RndMnkIII/Analogizer/case_mounting/1722326016145.jpg

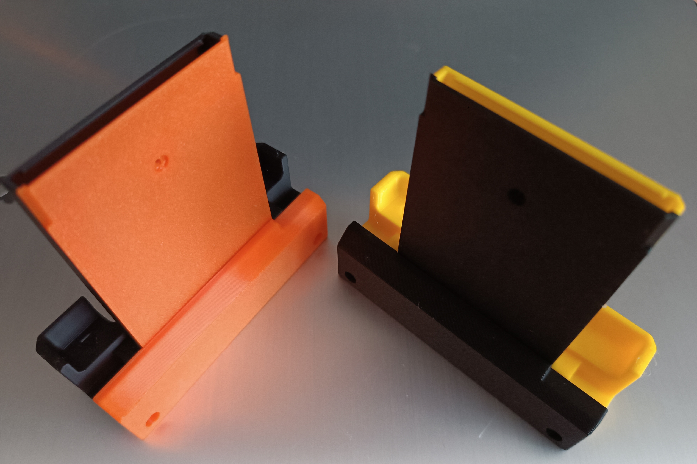
case_mounting/1722326016145.jpg
