RndMnkIII/Analogizer/case_mounting/1722326016159.jpg

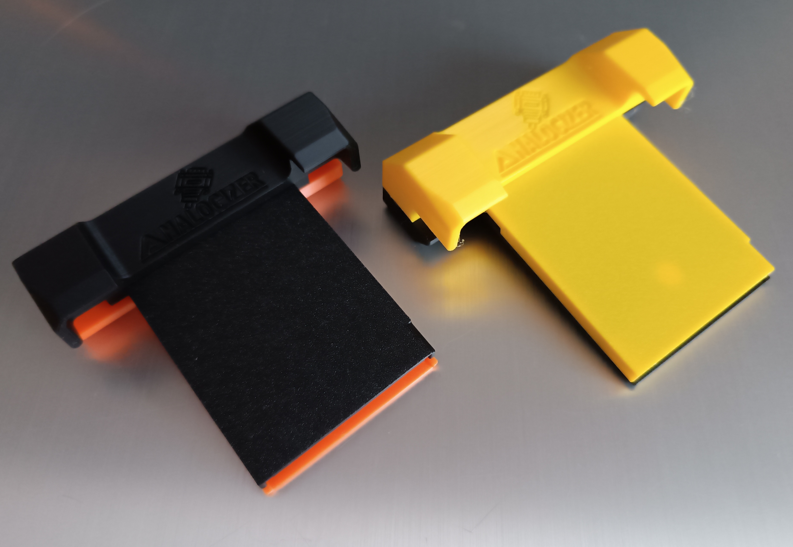
case_mounting/1722326016159.jpg
