RndMnkIII/Analogizer/case_mounting/1722326016175.jpg

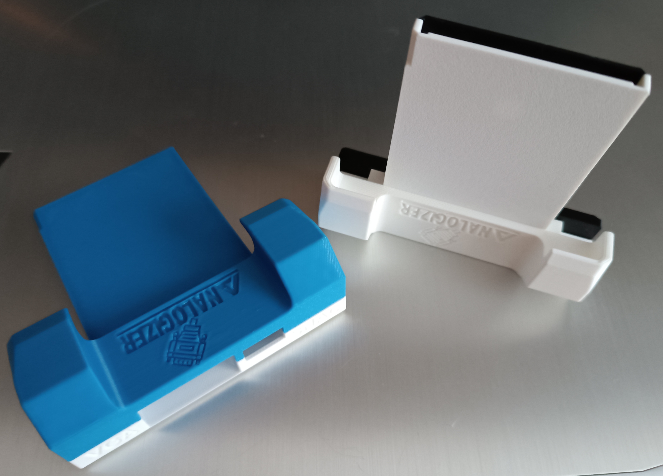
case_mounting/1722326016175.jpg
