RndMnkIII/Analogizer/case_mounting/1722326016191.jpg

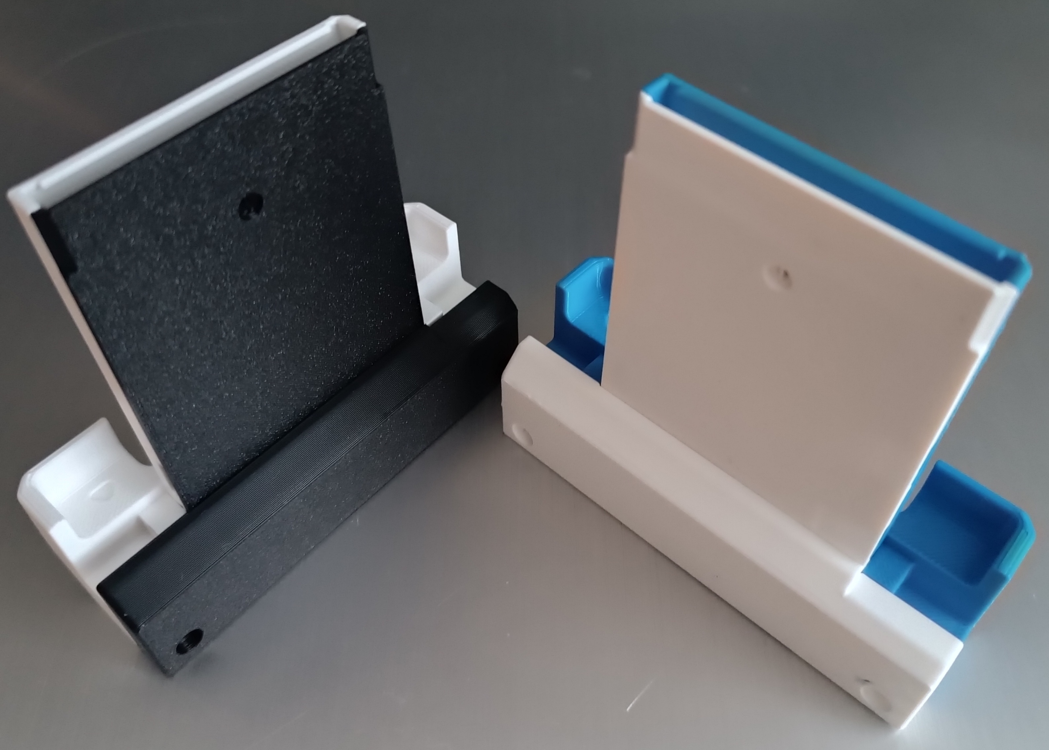
case_mounting/1722326016191.jpg
