RndMnkIII/Analogizer/case_mounting/1722326016210.jpg

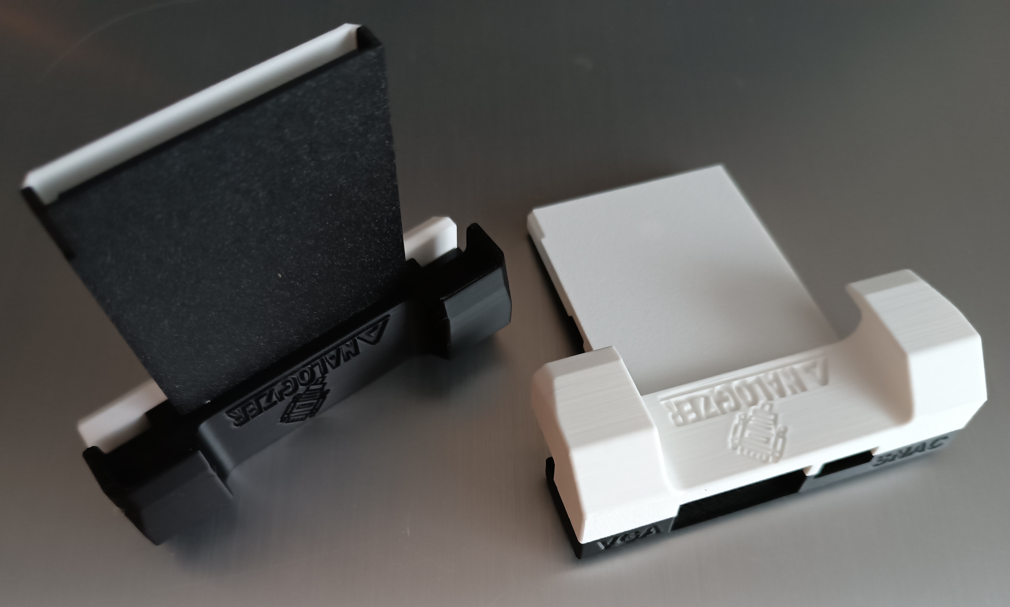
case_mounting/1722326016210.jpg
