RndMnkIII/Analogizer/case_mounting/1722352187809.jpg

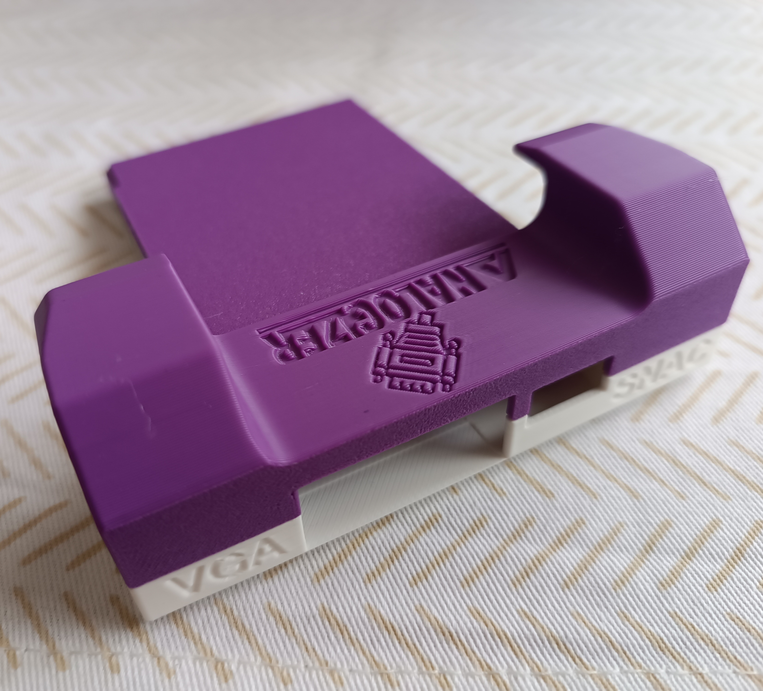
case_mounting/1722352187809.jpg
