RndMnkIII/Analogizer/case_mounting/1722352187818.jpg

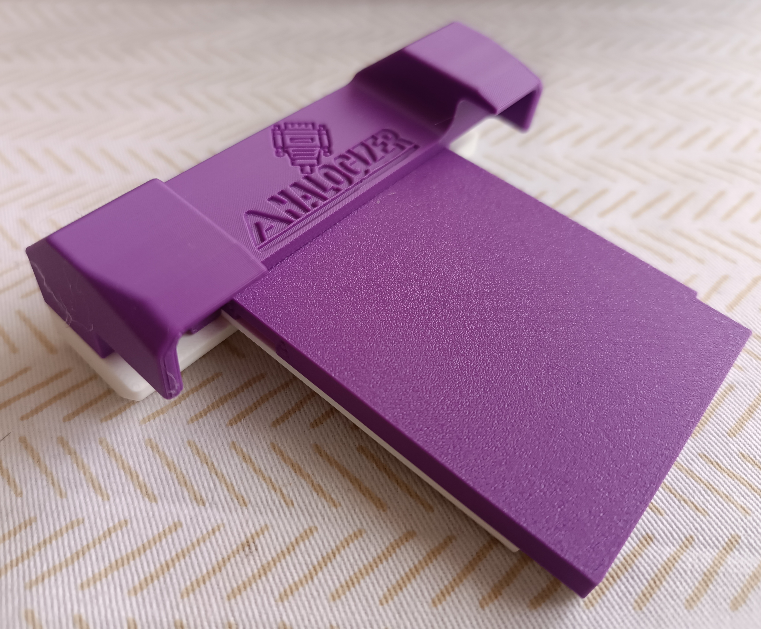
case_mounting/1722352187818.jpg
