RndMnkIII/Analogizer/case_mounting/1722352187828.jpg

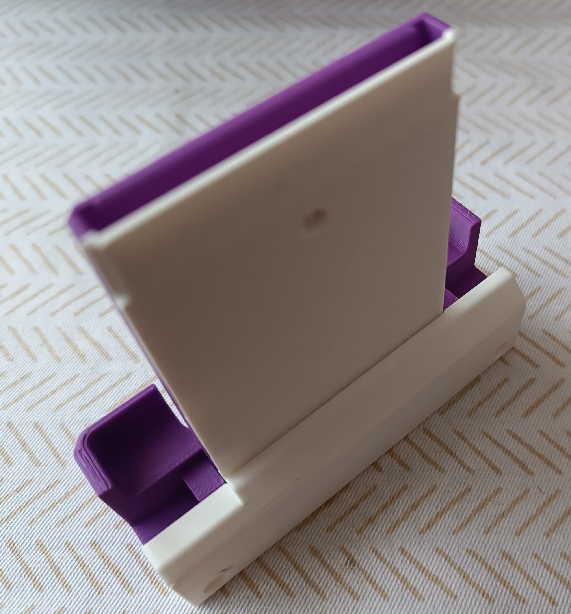
case_mounting/1722352187828.jpg
