RndMnkIII/Analogizer/case_mounting/1722354113847.jpg

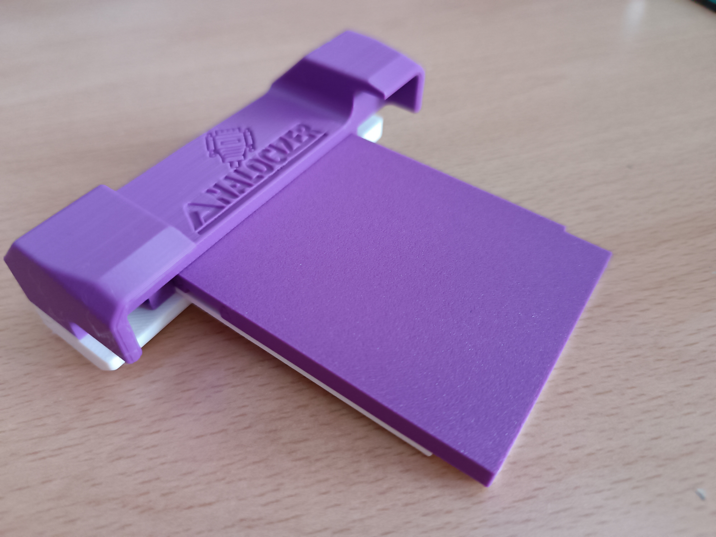
case_mounting/1722354113847.jpg
