RndMnkIII/Analogizer/case_mounting/1722354113891.jpg

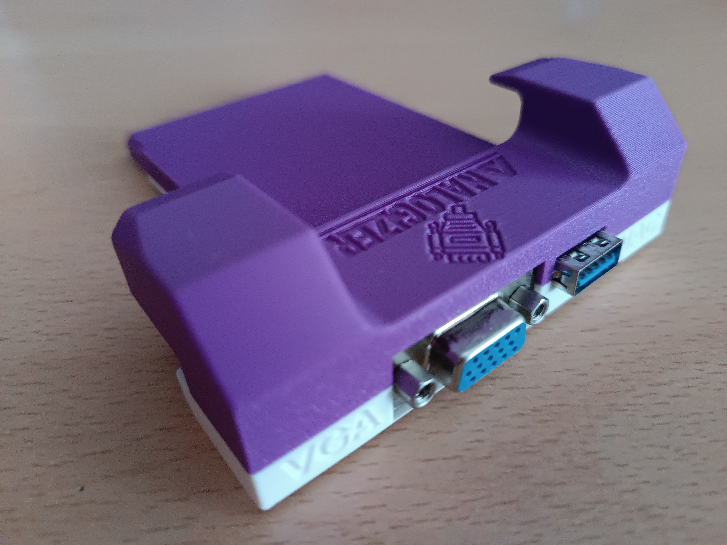
case_mounting/1722354113891.jpg
