RndMnkIII/Analogizer/hardware/SCH/PCENGINE_CABLE_HARNESS_SCH.PNG

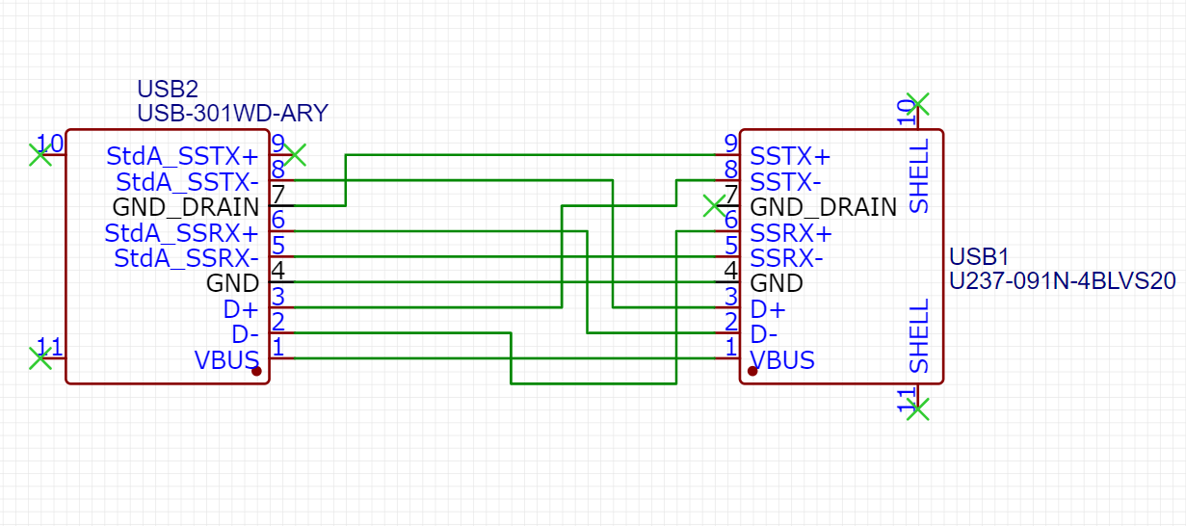
hardware/SCH/PCENGINE_CABLE_HARNESS_SCH.PNG
