RndMnkIII/Analogizer/hardware/SEGA_Genesis_Cable_harness/Captura de pantalla 2026-07-21 204106.png

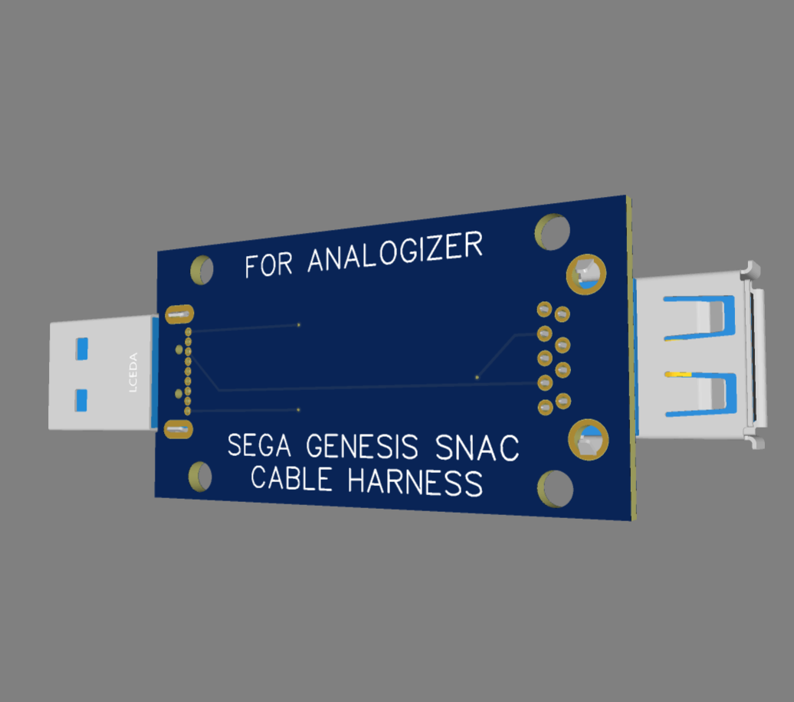
hardware/SEGA_Genesis_Cable_harness/Captura de pantalla 2026-07-21 204106.png
