RndMnkIII/Analogizer/hardware/SEGA_Genesis_Cable_harness/schematic.png

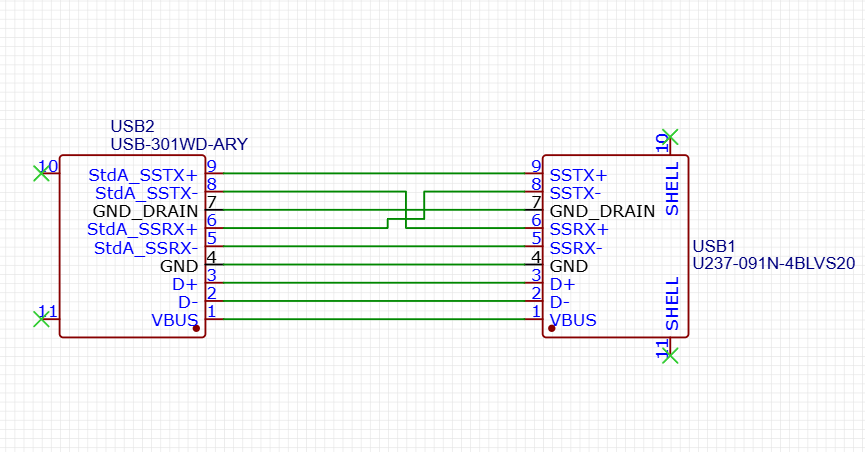
hardware/SEGA_Genesis_Cable_harness/schematic.png
