RndMnkIII/Analogizer/img/3D_PCB_HARNESS.PNG

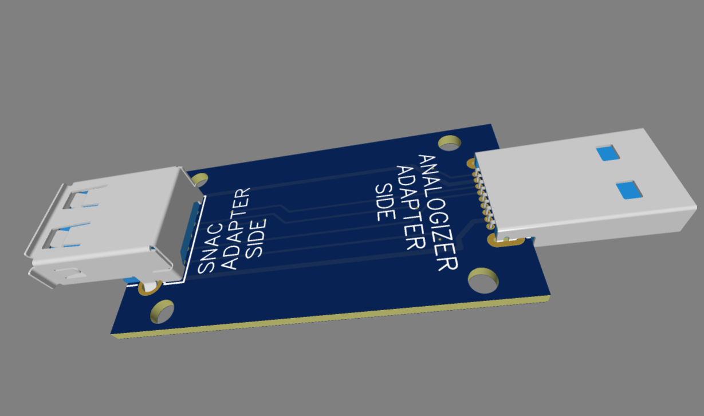
img/3D_PCB_HARNESS.PNG
