RndMnkIII/Analogizer/img/1710557132168.jpg

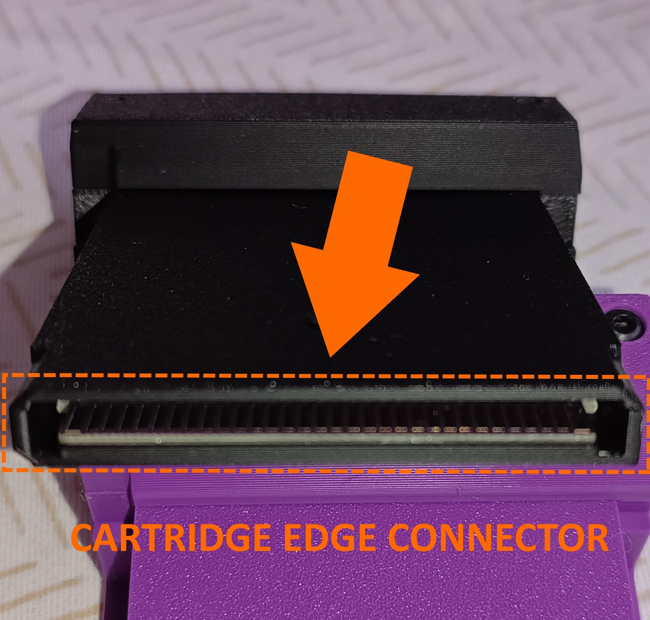
img/1710557132168.jpg
