RndMnkIII/Analogizer/img/1711795943821.jpg

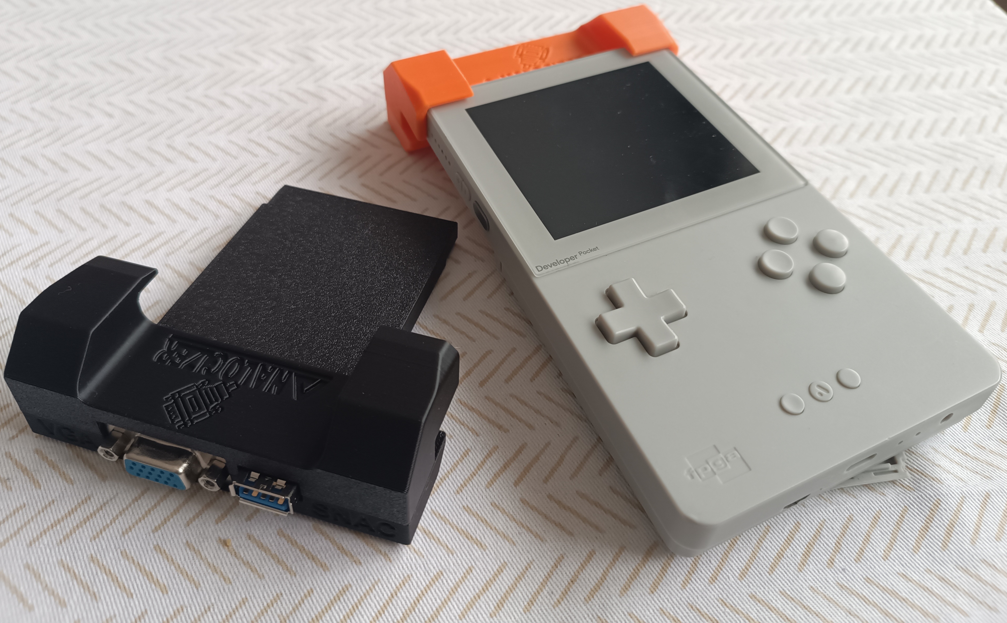
img/1711795943821.jpg
