RndMnkIII/Analogizer/img/1712216898707.jpg

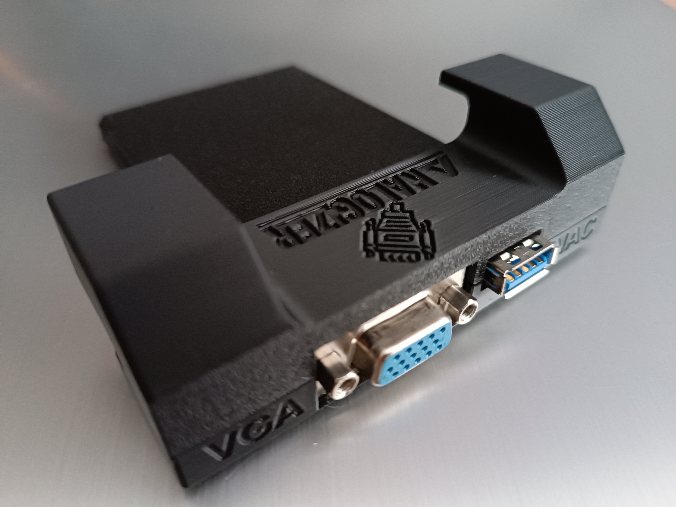
img/1712216898707.jpg
