RndMnkIII/Analogizer/img/1713608049392.jpg

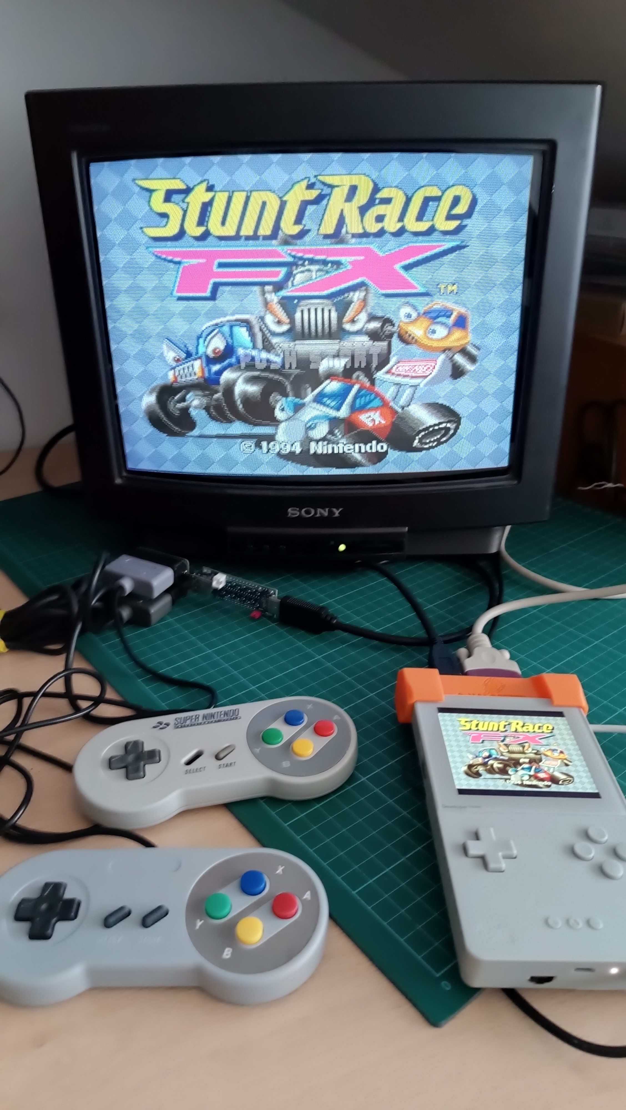
img/1713608049392.jpg
