RndMnkIII/Analogizer/img/1719057492224.jpg

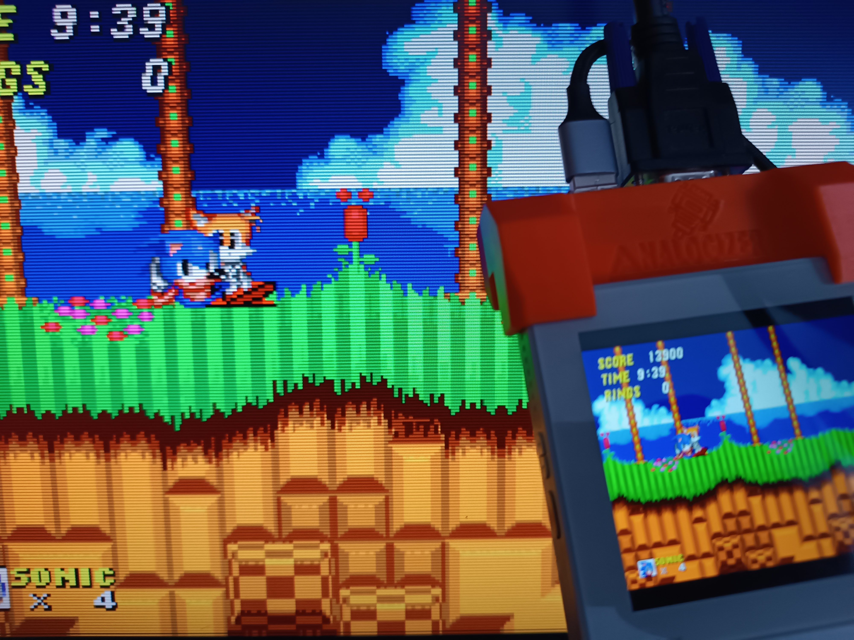
img/1719057492224.jpg
