RndMnkIII/Analogizer/img/1738831503520.jpg

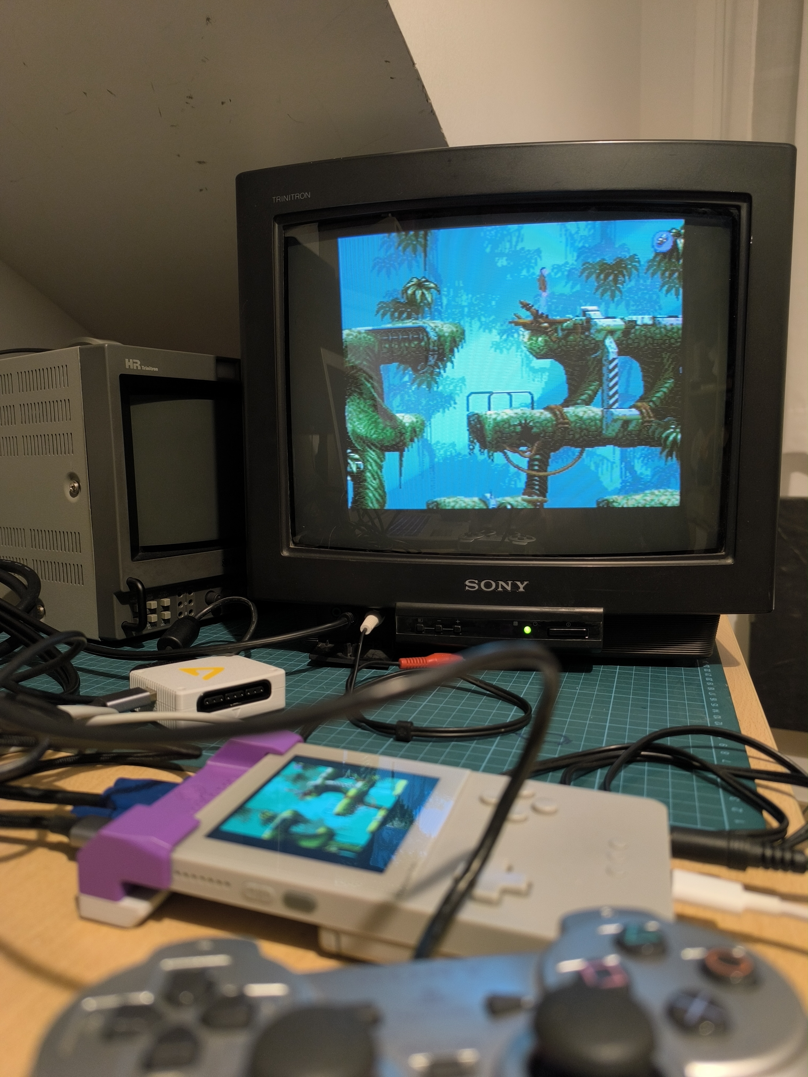
img/1738831503520.jpg
