RndMnkIII/Analogizer/img/A_nalogizer.png

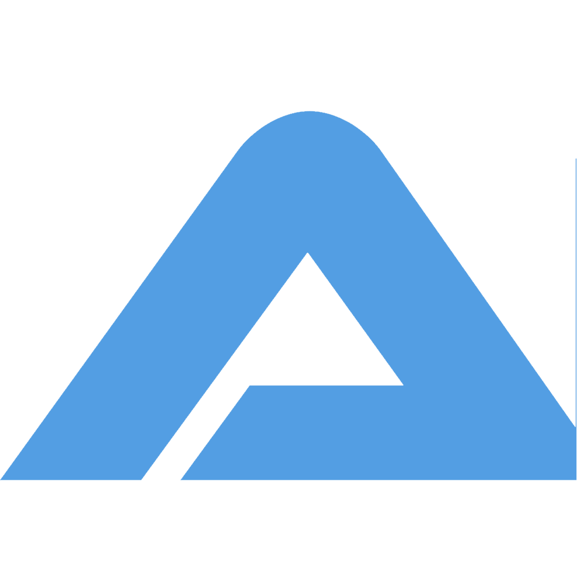
img/A_nalogizer.png
