RndMnkIII/Analogizer/img/ANALOGIZER_FRONT_SIDE.jpg

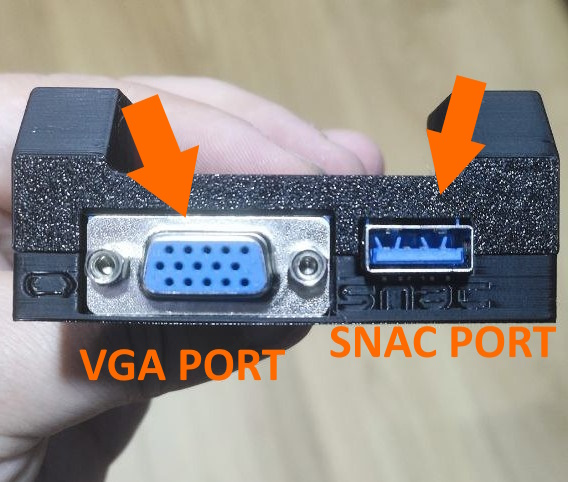
img/ANALOGIZER_FRONT_SIDE.jpg
