RndMnkIII/Analogizer/img/ANALOGIZER_SWITCH_AB.jpg

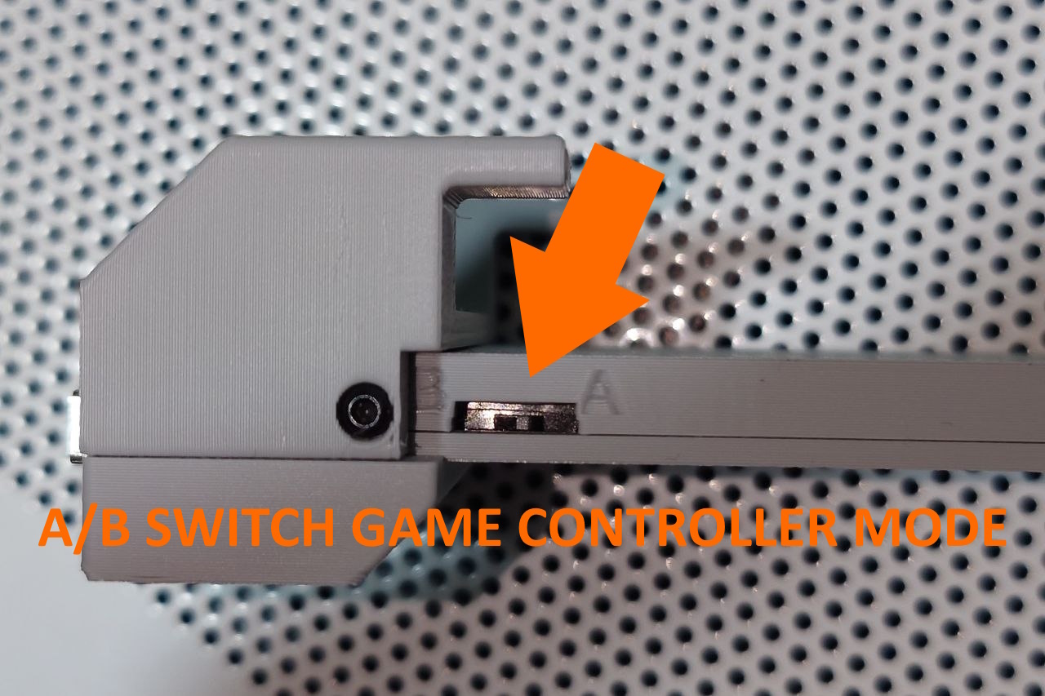
img/ANALOGIZER_SWITCH_AB.jpg
