RndMnkIII/Analogizer/img/ANALOGIZER_USB_C_PWR.jpg

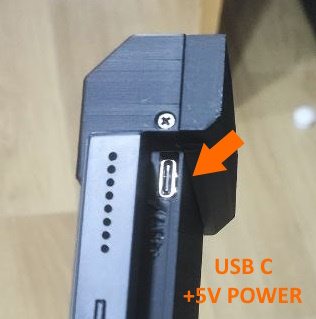
img/ANALOGIZER_USB_C_PWR.jpg
