RndMnkIII/Analogizer/img/antonio_villena_SNAC7_USB3_ADAPTERS.jpg

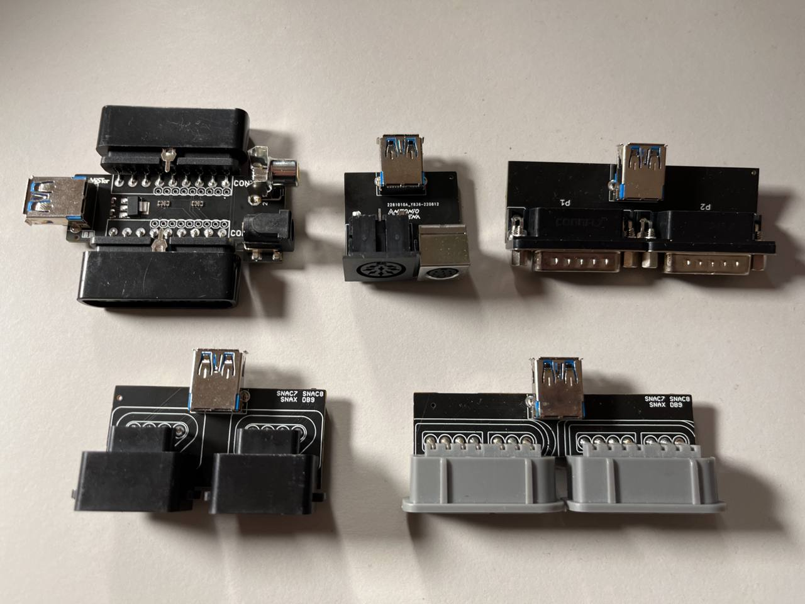
img/antonio_villena_SNAC7_USB3_ADAPTERS.jpg
