RndMnkIII/Analogizer/img/audio_jack.png

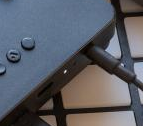
img/audio_jack.png
