RndMnkIII/Analogizer/img/cable_RGB_LINE_AUDIO_TO_SCART.PNG

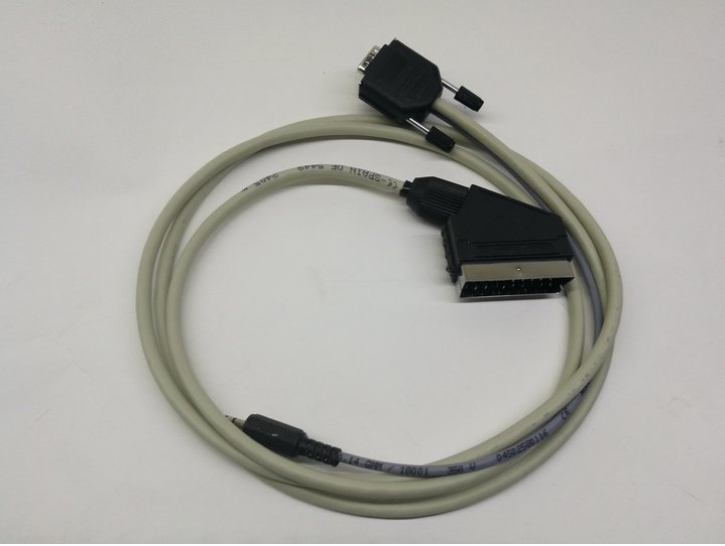
img/cable_RGB_LINE_AUDIO_TO_SCART.PNG
