RndMnkIII/Analogizer/img/como_conectar_cable_harness.jpg

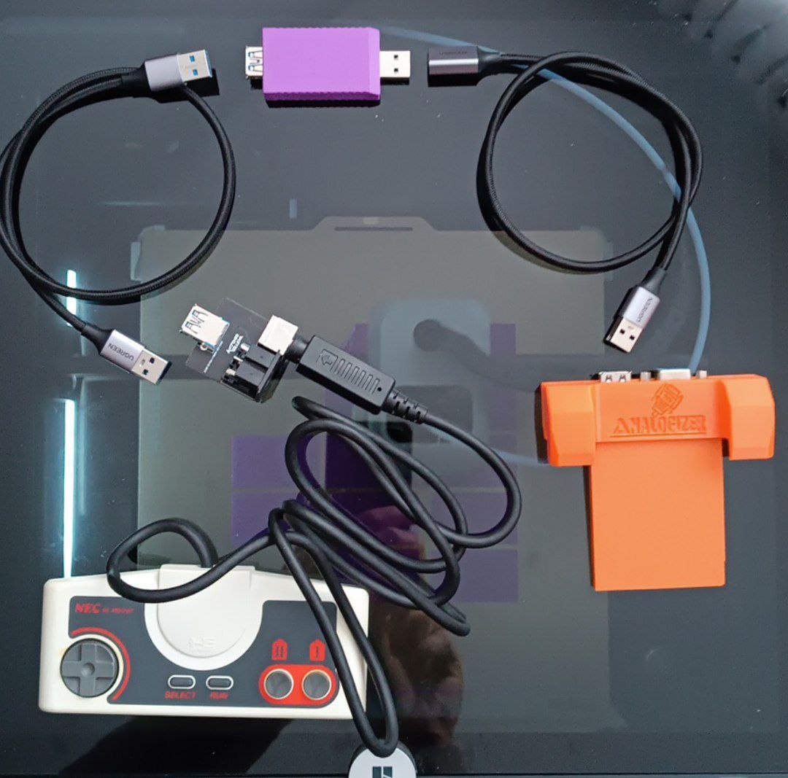
img/como_conectar_cable_harness.jpg
