RndMnkIII/Analogizer/img/cps1_analogizer.jpg

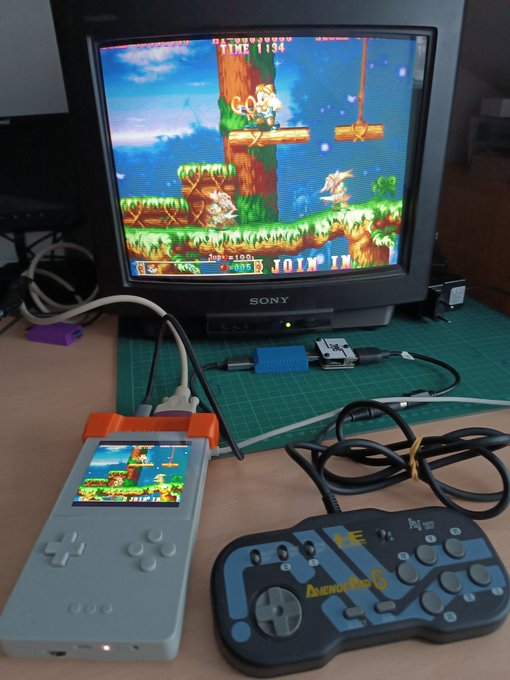
img/cps1_analogizer.jpg
