RndMnkIII/Analogizer/img/GanGeek_Style_video.png

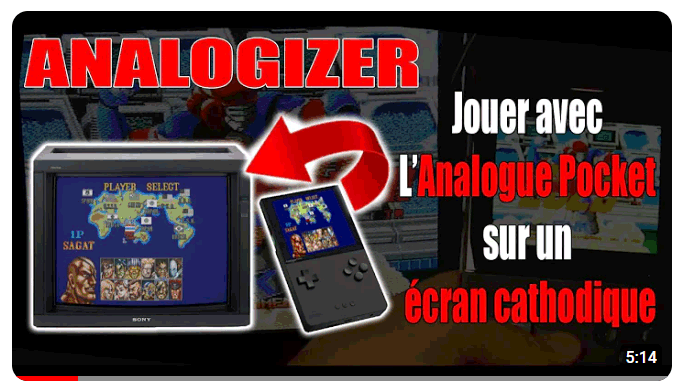
img/GanGeek_Style_video.png
