RndMnkIII/Analogizer/img/INSERT1.jpg

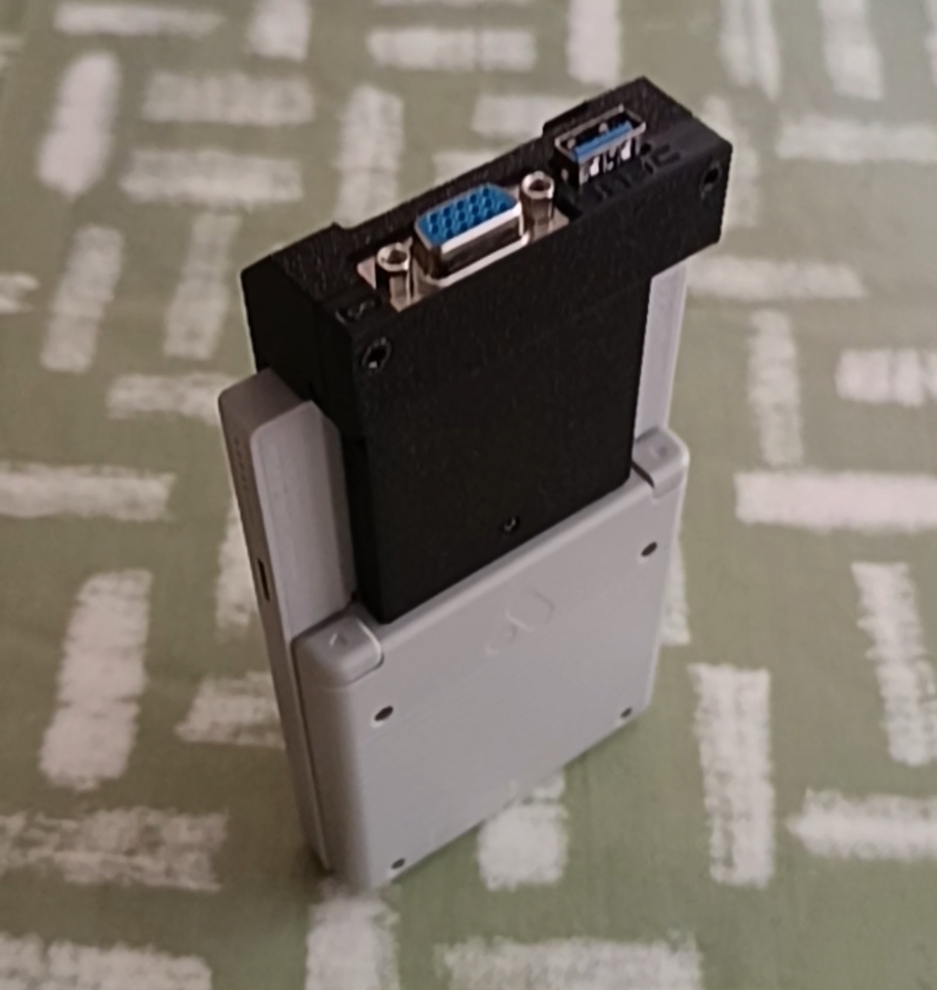
img/INSERT1.jpg
