RndMnkIII/Analogizer/img/INSERT2.jpg

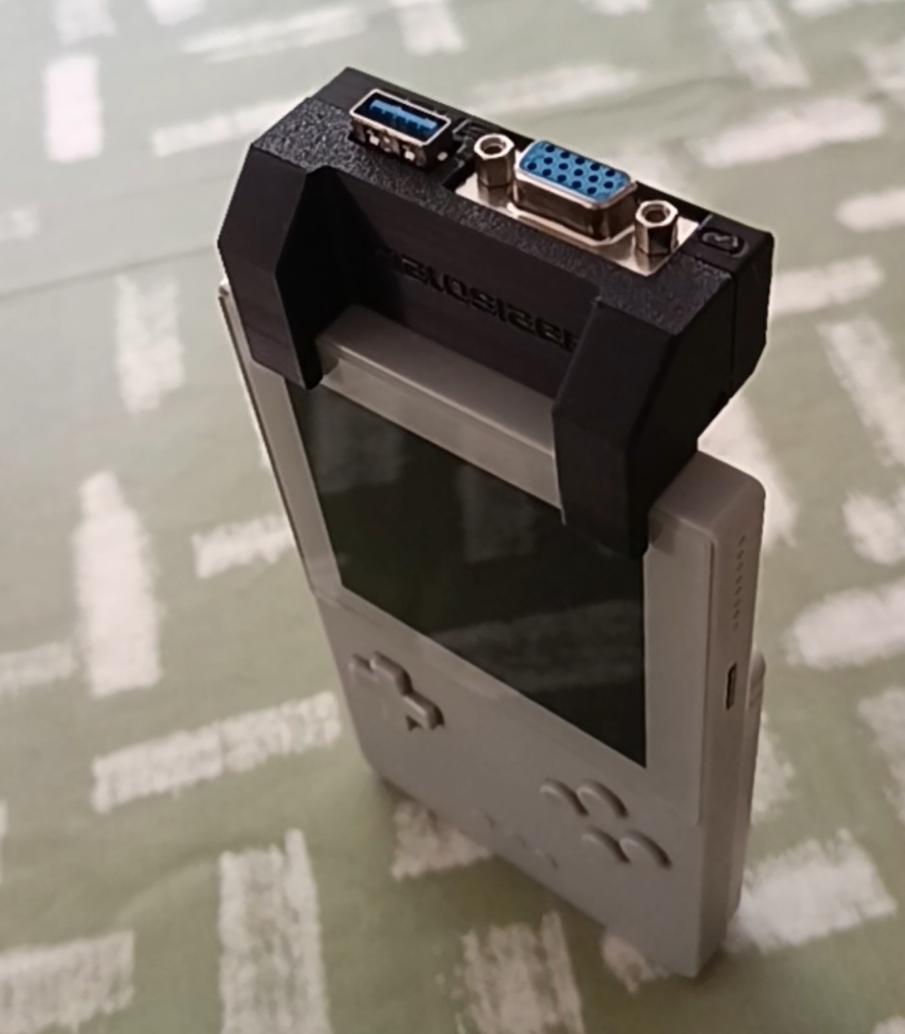
img/INSERT2.jpg
