RndMnkIII/Analogizer/img/iñaki video.png

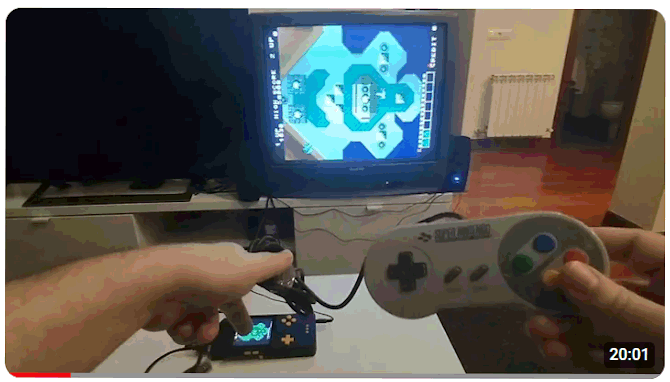
img/iñaki video.png
