RndMnkIII/Analogizer/img/PCENGINE_CABLE_HARNESS.jpg

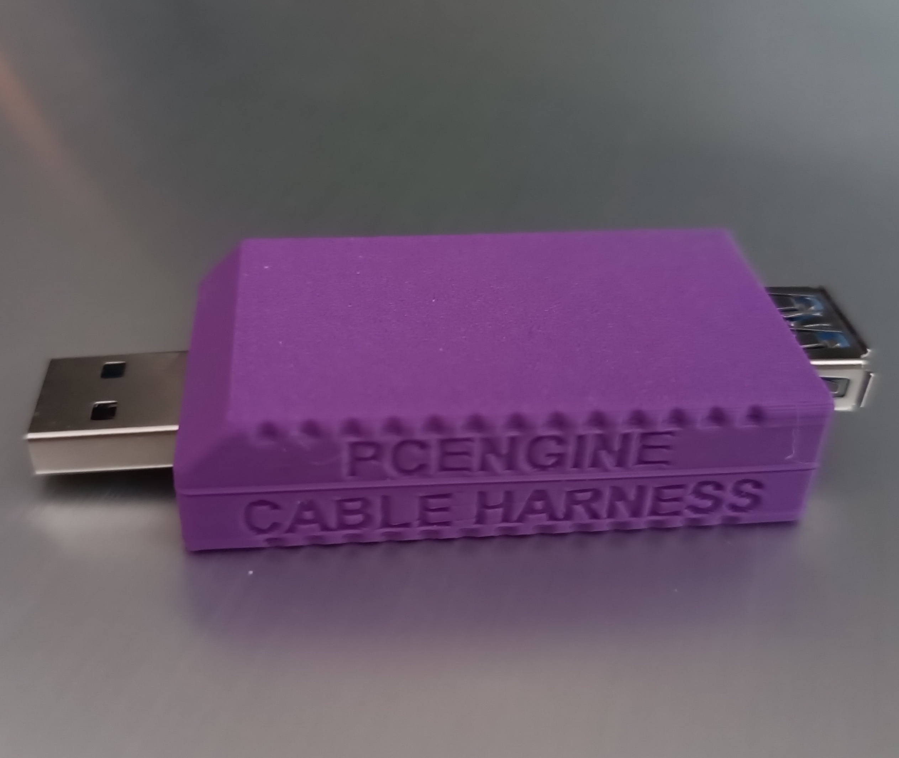
img/PCENGINE_CABLE_HARNESS.jpg
