RndMnkIII/Analogizer/img/PCENGINE_SNAC_HARNESS.png

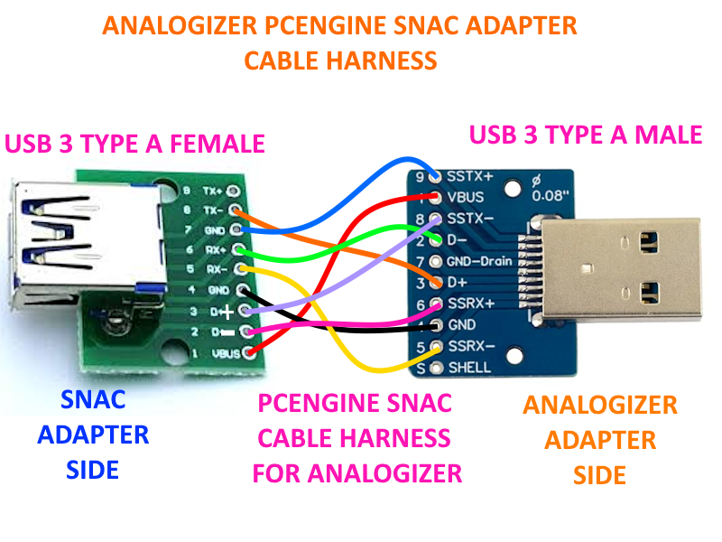
img/PCENGINE_SNAC_HARNESS.png
