RndMnkIII/Analogizer/img/PCN video.png

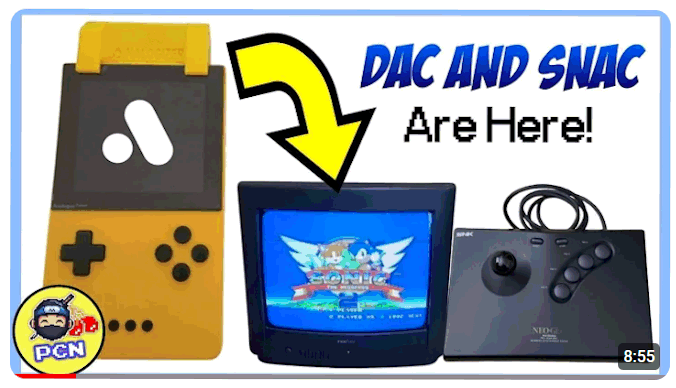
img/PCN video.png
