RndMnkIII/Analogizer/img/photo_5956438909166665243_y.jpg

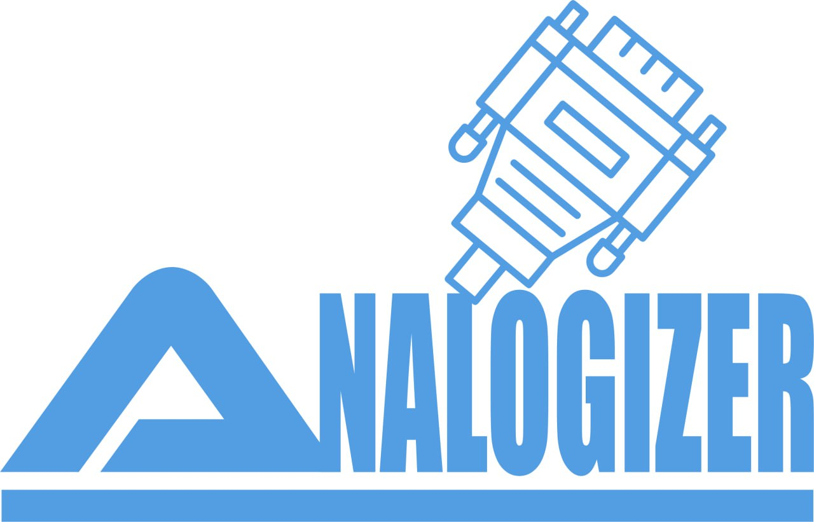
img/photo_5956438909166665243_y.jpg
