RndMnkIII/Analogizer/img/PSX_SNAC_LIGHT_GRAY_01.webp

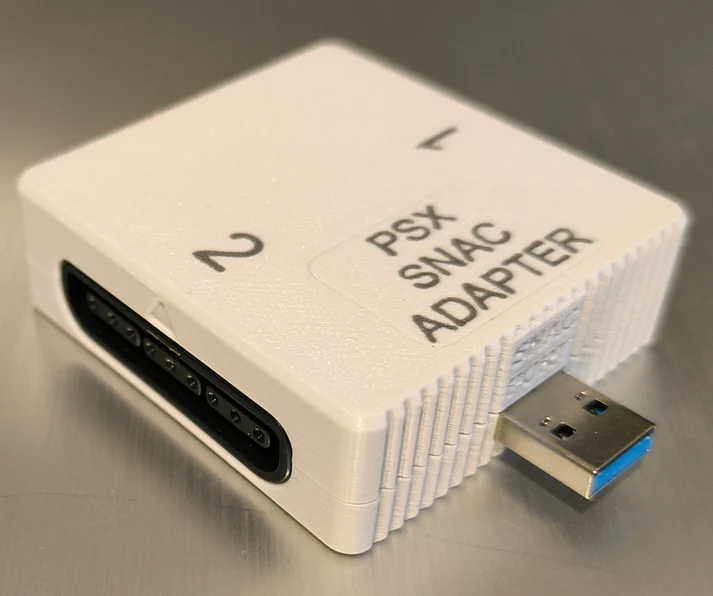
img/PSX_SNAC_LIGHT_GRAY_01.webp
