RndMnkIII/Analogizer/img/PSX_SNAC_LIGHT_GRAY_02.jpg

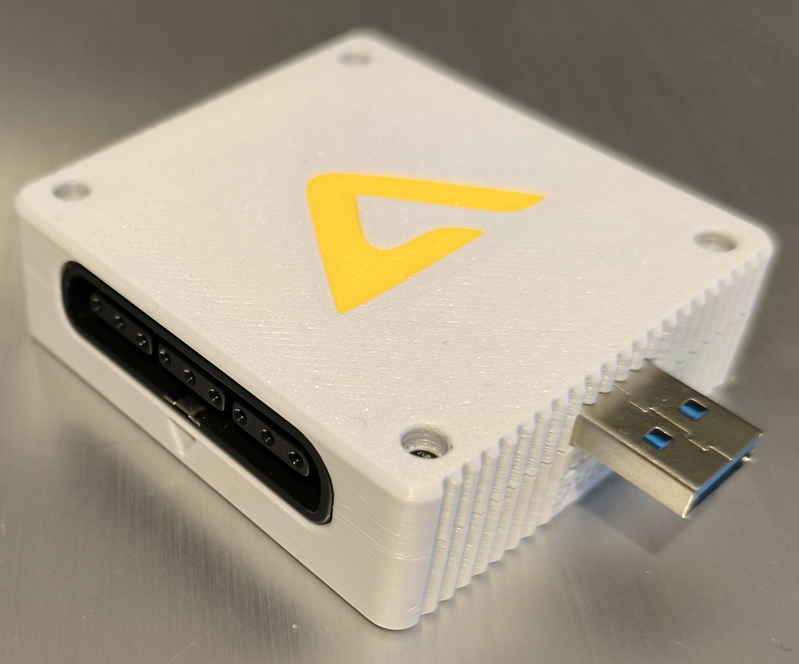
img/PSX_SNAC_LIGHT_GRAY_02.jpg
