RndMnkIII/Analogizer/img/RGBS_TO_YPBPR.jpg

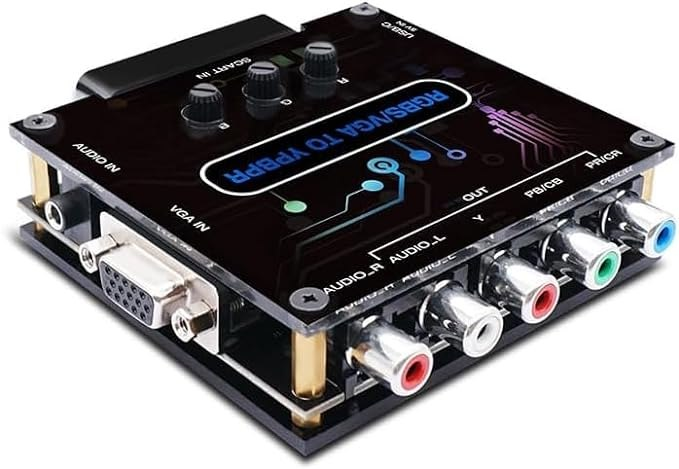
img/RGBS_TO_YPBPR.jpg
