RndMnkIII/Analogizer/img/SNAC-HDMI-2X-scaled.webp

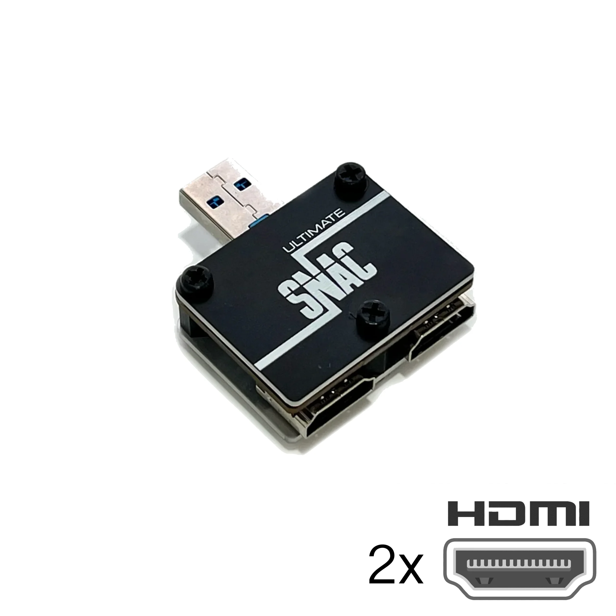
img/SNAC-HDMI-2X-scaled.webp
