RndMnkIII/Analogizer/img/SNAC_DB15_Antonio_Villena.jpg

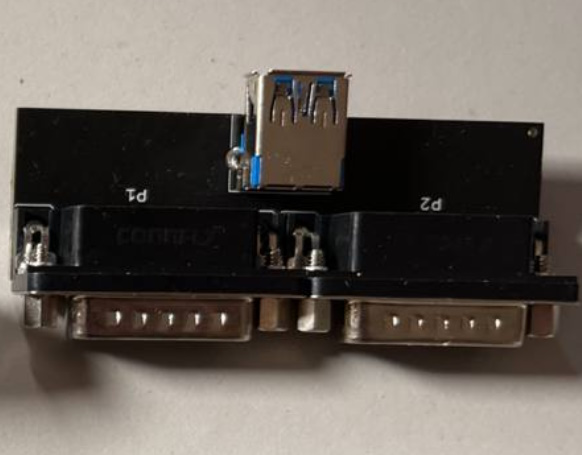
img/SNAC_DB15_Antonio_Villena.jpg
