RndMnkIII/Analogizer/img/SNAC_DB15_Splitter_UltimateMister.png

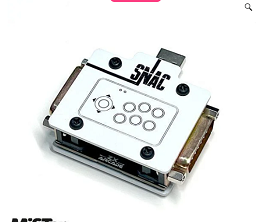
img/SNAC_DB15_Splitter_UltimateMister.png
