RndMnkIII/Analogizer/img/SNAC_NES_Single_Manuferhi.png

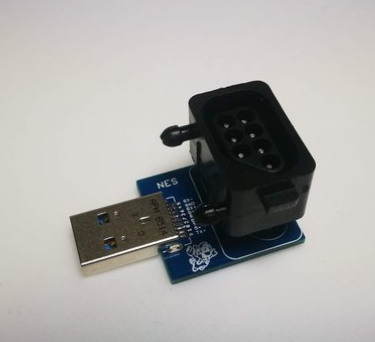
img/SNAC_NES_Single_Manuferhi.png
