RndMnkIII/Analogizer/img/SNAC_NES_Splitter_Antonio_Villena.jpg

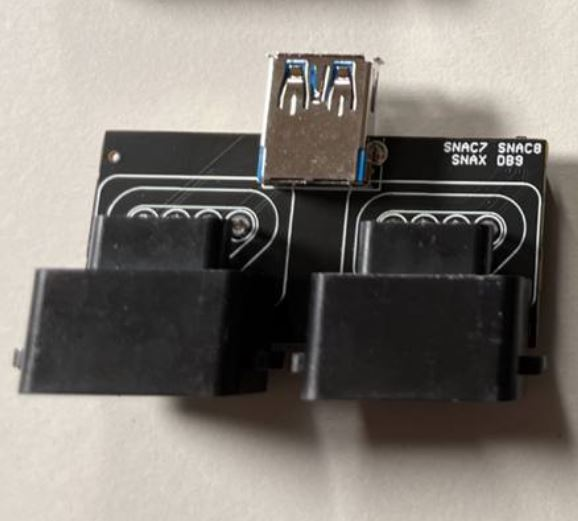
img/SNAC_NES_Splitter_Antonio_Villena.jpg
