RndMnkIII/Analogizer/img/SNAC_NES_Splitter_UltimateMister.png

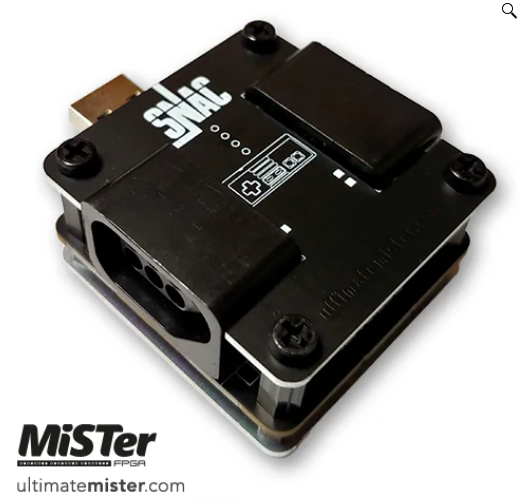
img/SNAC_NES_Splitter_UltimateMister.png
