RndMnkIII/Analogizer/img/SNAC_PCEngine_Antonio_Villena.jpg

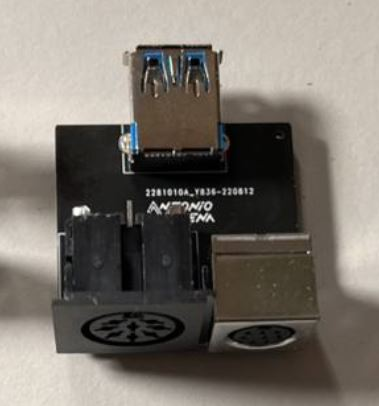
img/SNAC_PCEngine_Antonio_Villena.jpg
