RndMnkIII/Analogizer/img/SNAC_PCEngine_Single_Manuferhi.png

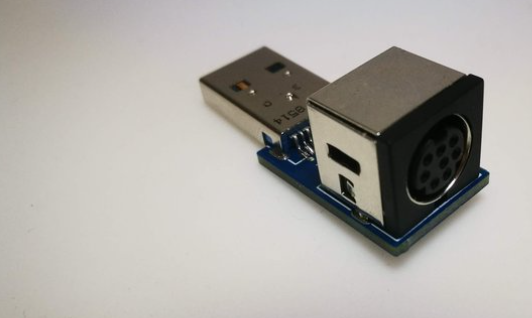
img/SNAC_PCEngine_Single_Manuferhi.png
