RndMnkIII/Analogizer/img/SNAC_SNES_Single_Manuferhi.png

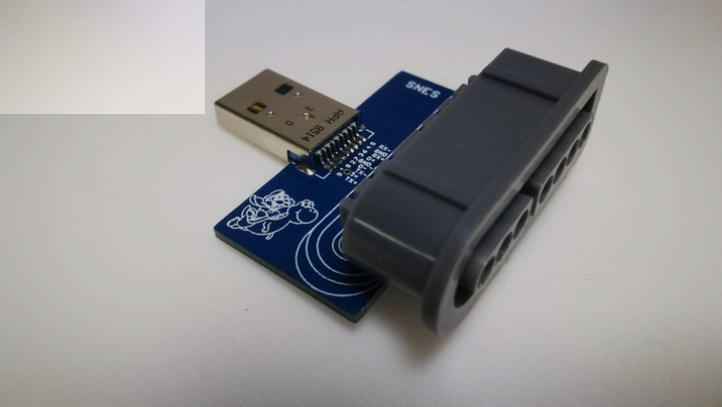
img/SNAC_SNES_Single_Manuferhi.png
