RndMnkIII/Analogizer/img/SNAC_SNES_Splitter_Antonio_Villena.jpg

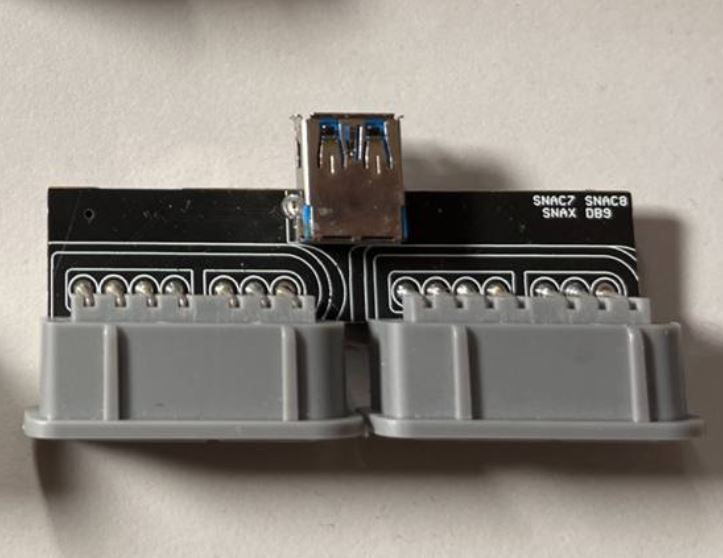
img/SNAC_SNES_Splitter_Antonio_Villena.jpg
