RndMnkIII/Analogizer/img/SOG.jpg

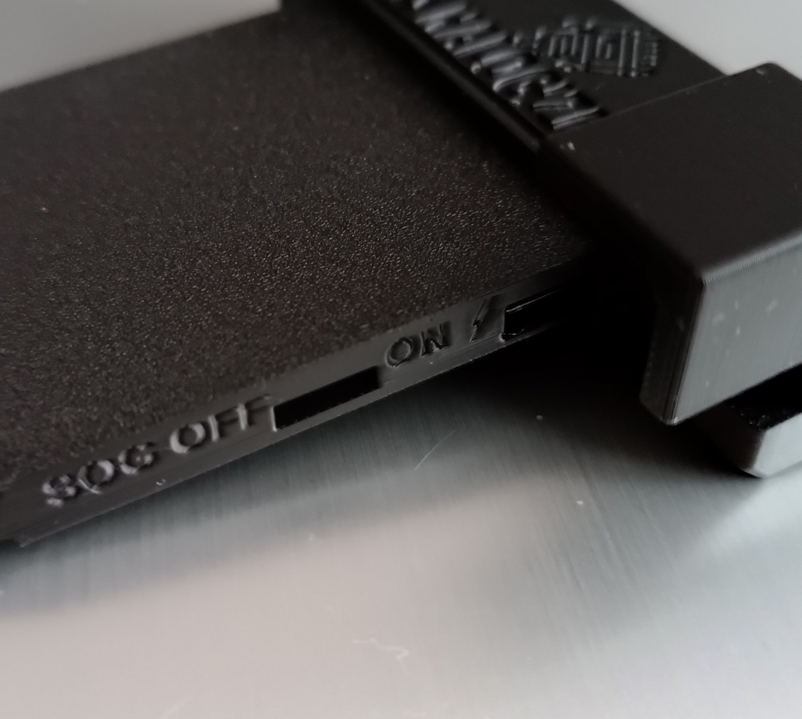
img/SOG.jpg
