RndMnkIII/Analogizer/img/sunset_raiders_captura.PNG

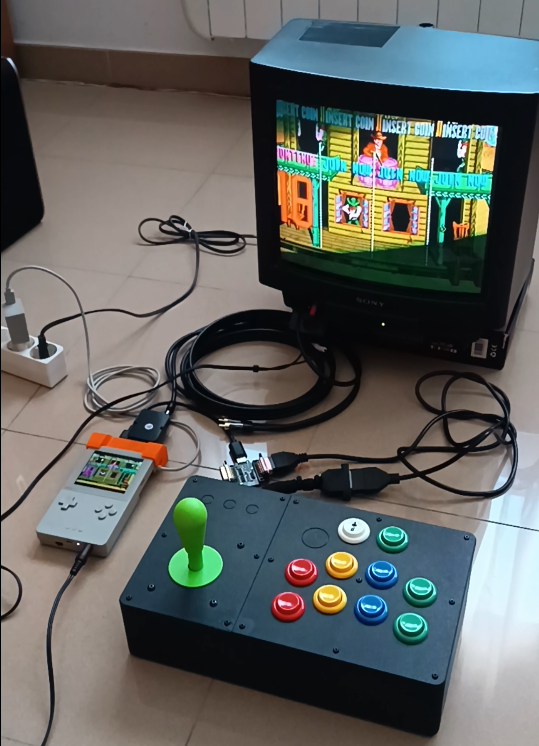
img/sunset_raiders_captura.PNG
