RndMnkIII/Analogizer/img/ultimate_mister_snes_snac.png

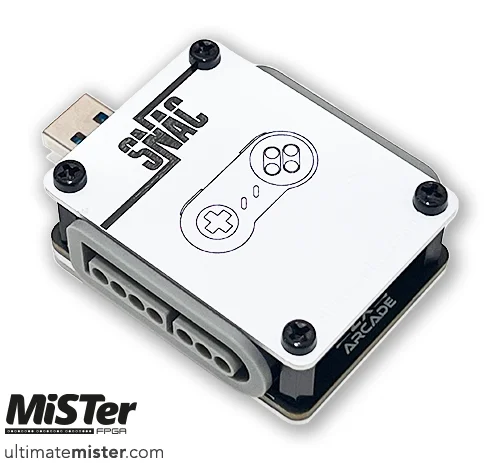
img/ultimate_mister_snes_snac.png
