RndMnkIII/Analogizer/img/USB3_TYPE-A_FEMALE.webp

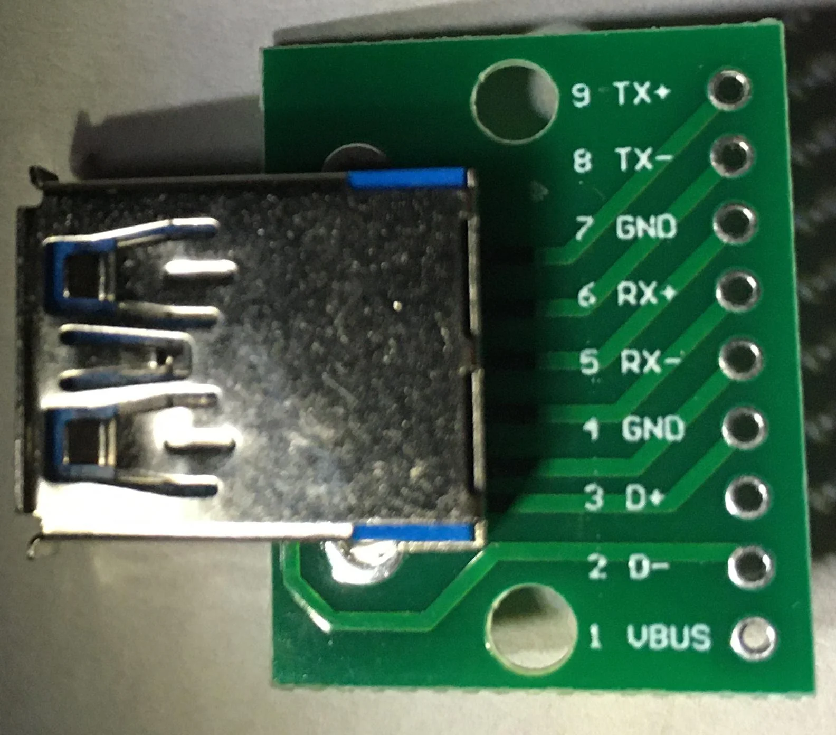
img/USB3_TYPE-A_FEMALE.webp
