RndMnkIII/Analogizer/img/USB_BREAKOUT_PCB.png

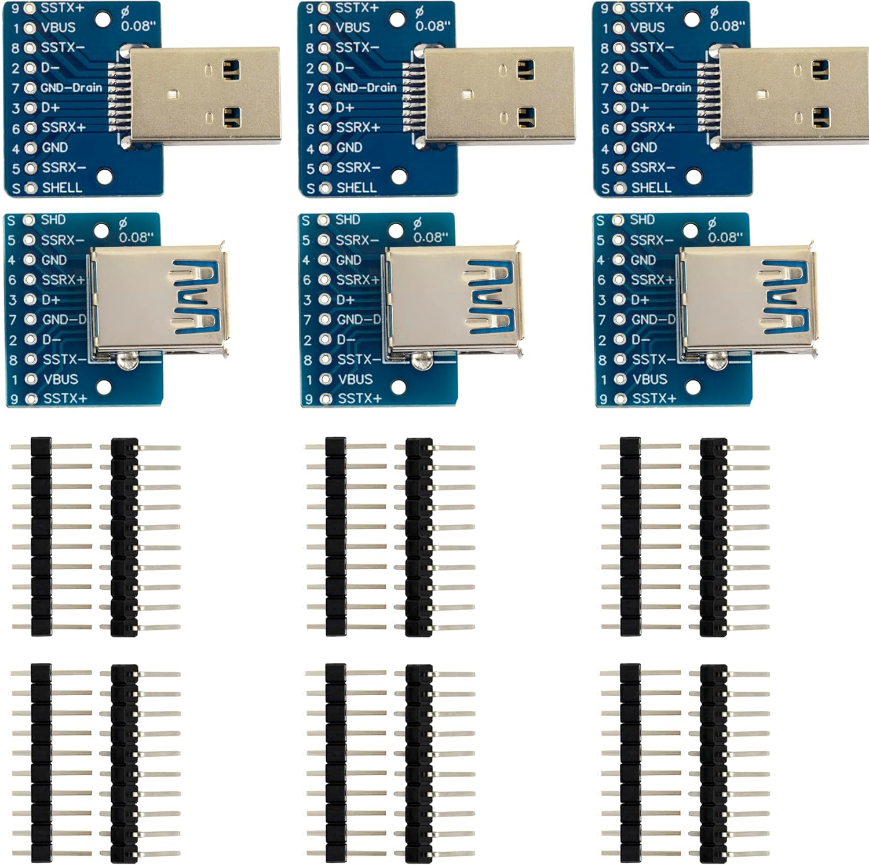
img/USB_BREAKOUT_PCB.png
