RndMnkIII/Analogizer/img/video_game_esoterica_video.png

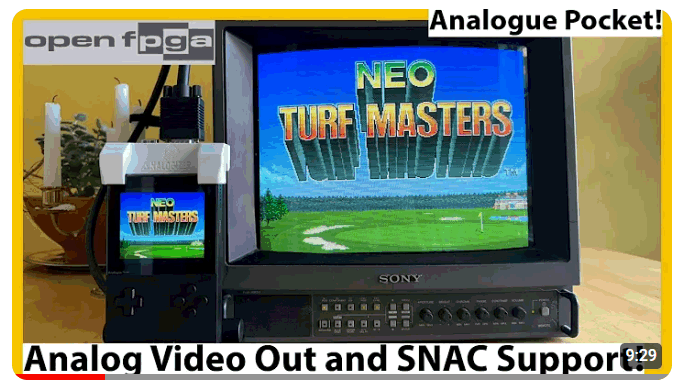
img/video_game_esoterica_video.png
