RndMnkIII/Analogizer/img/video_lu_retro.png

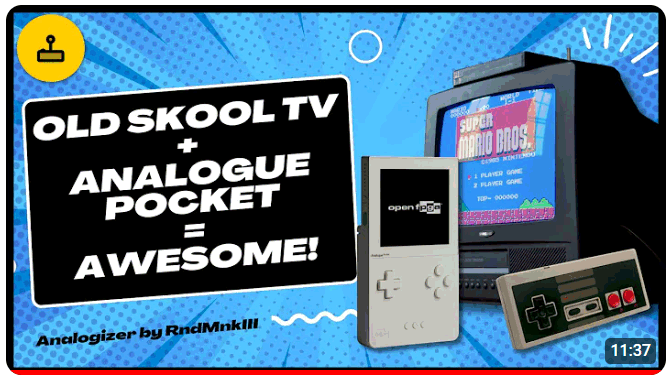
img/video_lu_retro.png
