RndMnkIII/Analogizer/img/video_marc_retro.png

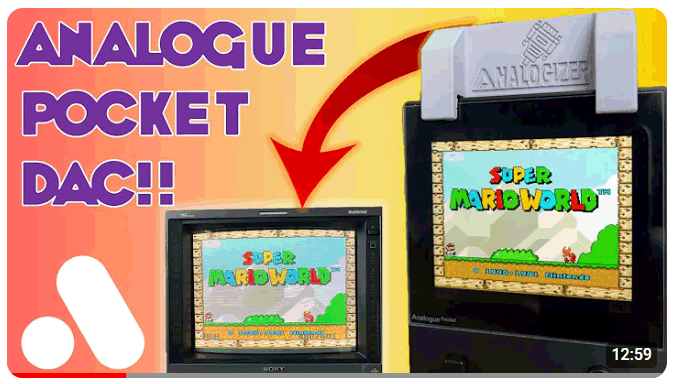
img/video_marc_retro.png
