RndMnkIII/Analogizer/img/WARNING.png

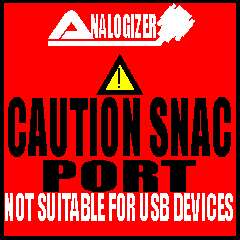
img/WARNING.png
