RndMnkIII/Analogizer/img/WARNING_HQ.png

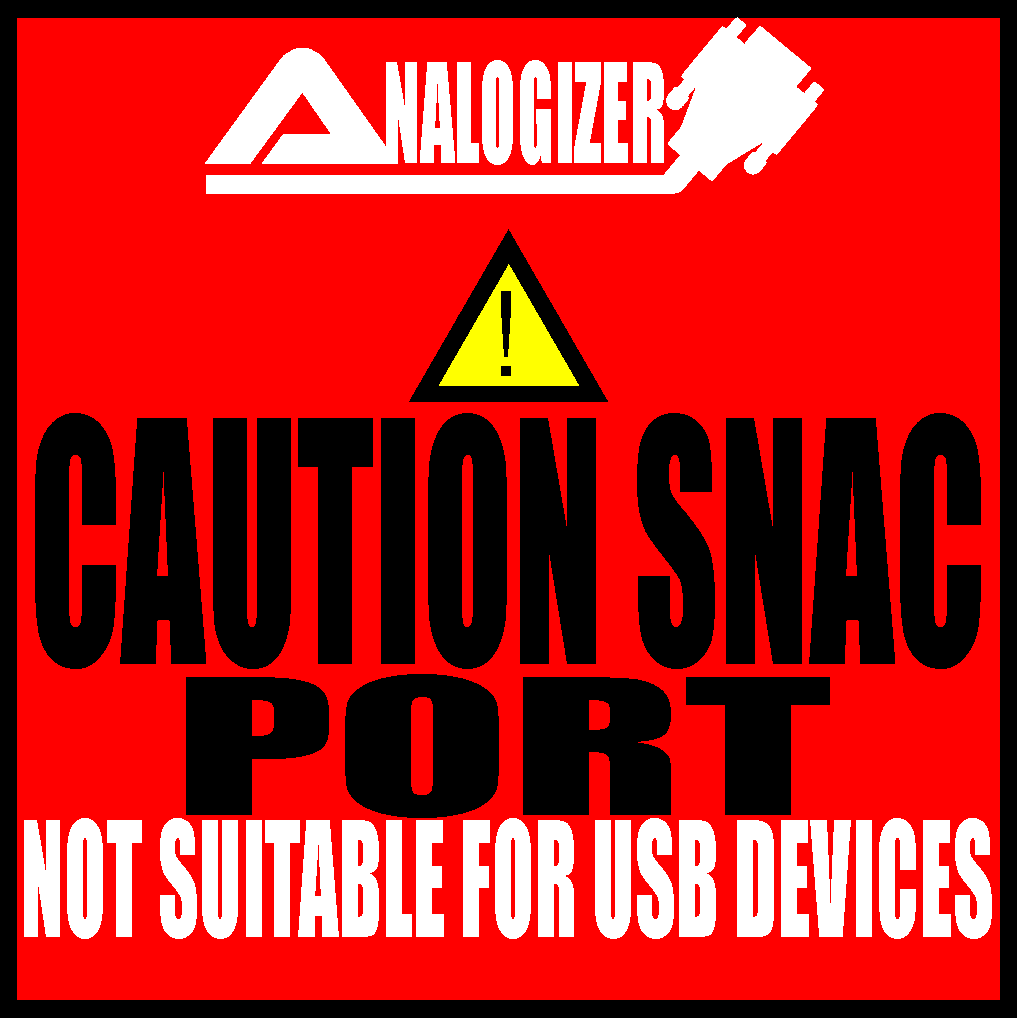
img/WARNING_HQ.png
