RndMnkIII/Analogizer/img/ypbpr_video_options.jpg

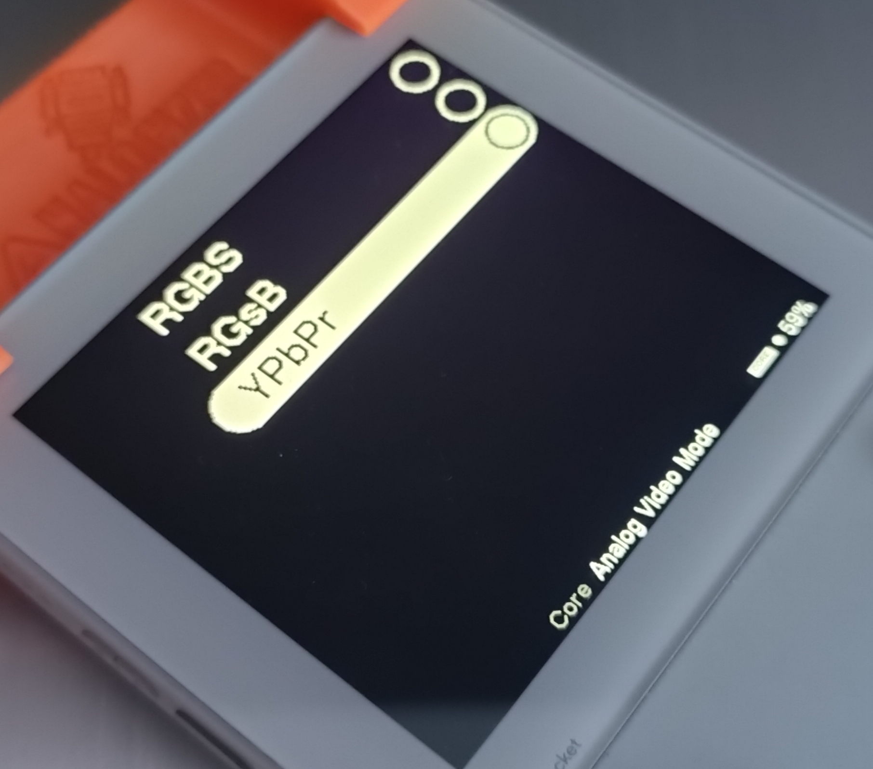
img/ypbpr_video_options.jpg
