RndMnkIII/Analogizer/case_mounting/Step00_ToolsA.jpg

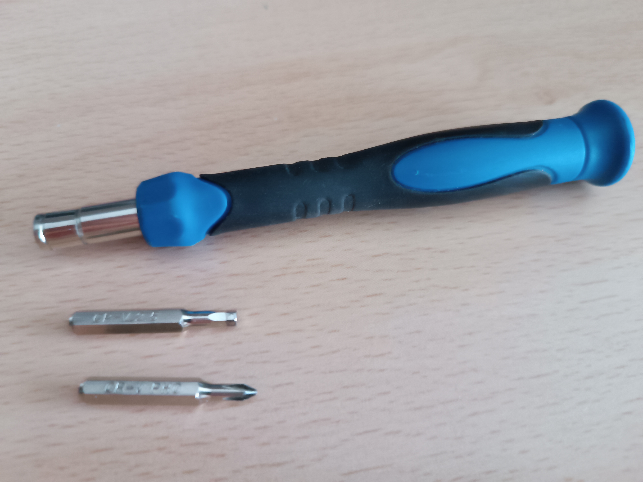
case_mounting/Step00_ToolsA.jpg
