RndMnkIII/Analogizer/case_mounting/Step00_ToolsB.jpg

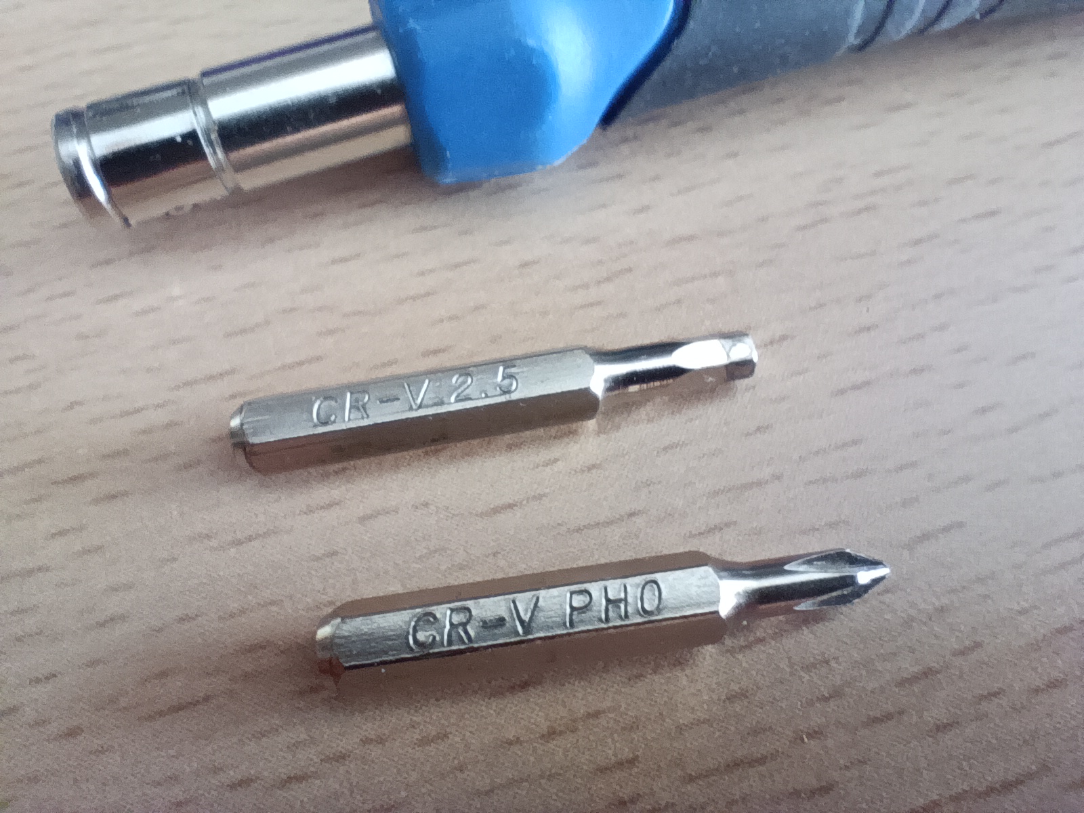
case_mounting/Step00_ToolsB.jpg
