RndMnkIII/Analogizer/case_mounting/Step03_Closing_PCB.jpg

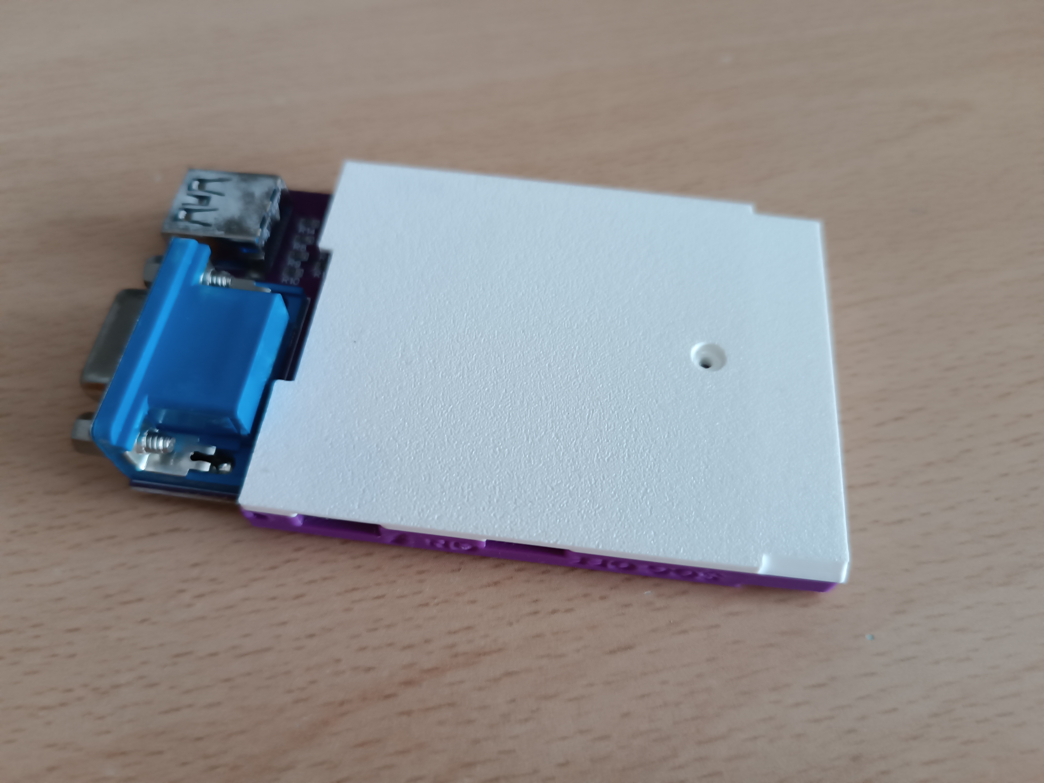
case_mounting/Step03_Closing_PCB.jpg
