RndMnkIII/Analogizer/case_mounting/Step05_Put_TOP_header_case_part.jpg

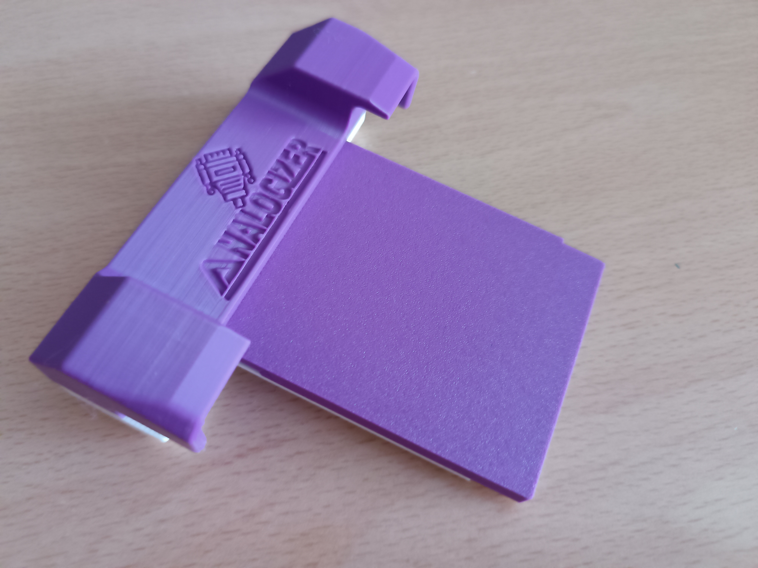
case_mounting/Step05_Put_TOP_header_case_part.jpg
