RndMnkIII/Analogizer/case_mounting/Step06_Screw PCB casing.jpg

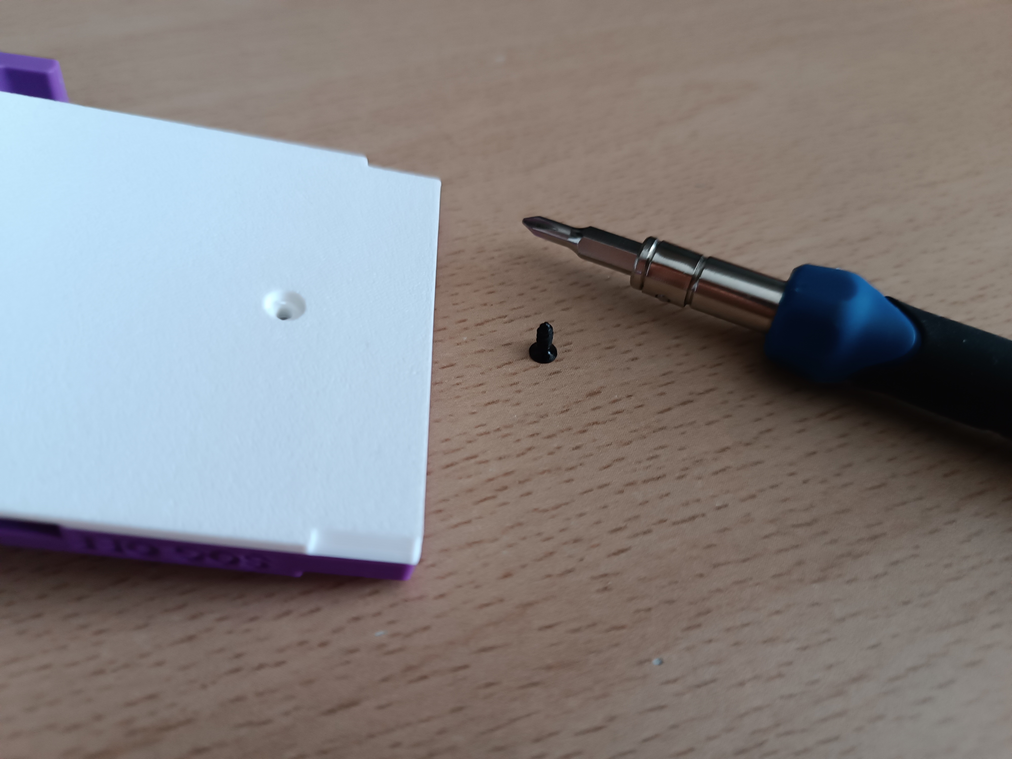
case_mounting/Step06_Screw PCB casing.jpg
