RndMnkIII/Analogizer/case_mounting/Step06_Screw PCB casingB.jpg

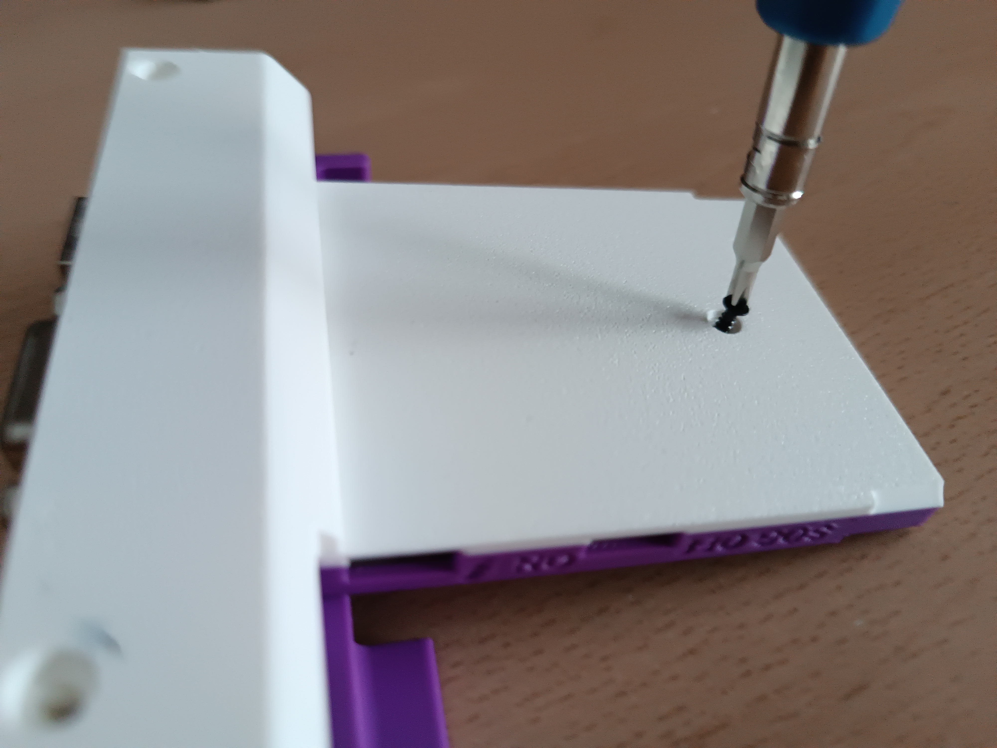
case_mounting/Step06_Screw PCB casingB.jpg
