RndMnkIII/Analogizer/case_mounting/Step06_Screw PCB casingC.jpg

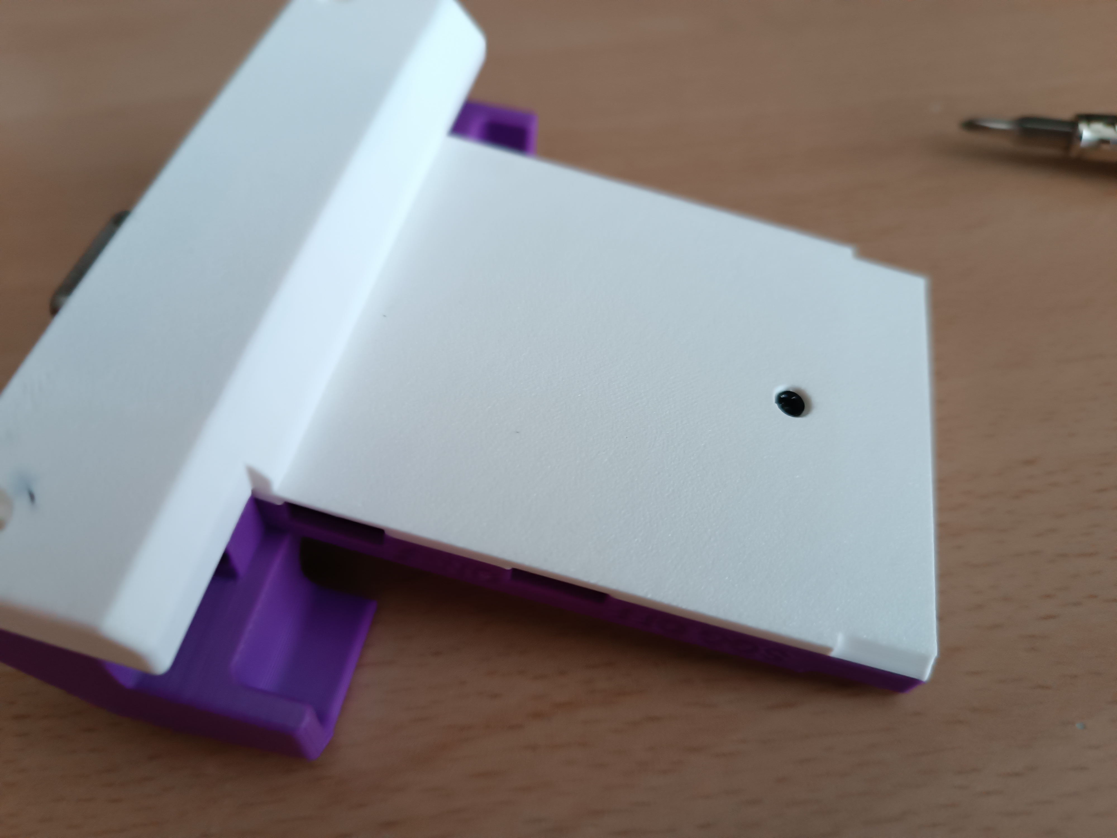
case_mounting/Step06_Screw PCB casingC.jpg
