RndMnkIII/Analogizer/case_mounting/Step07_Screw_case_sidesB.jpg

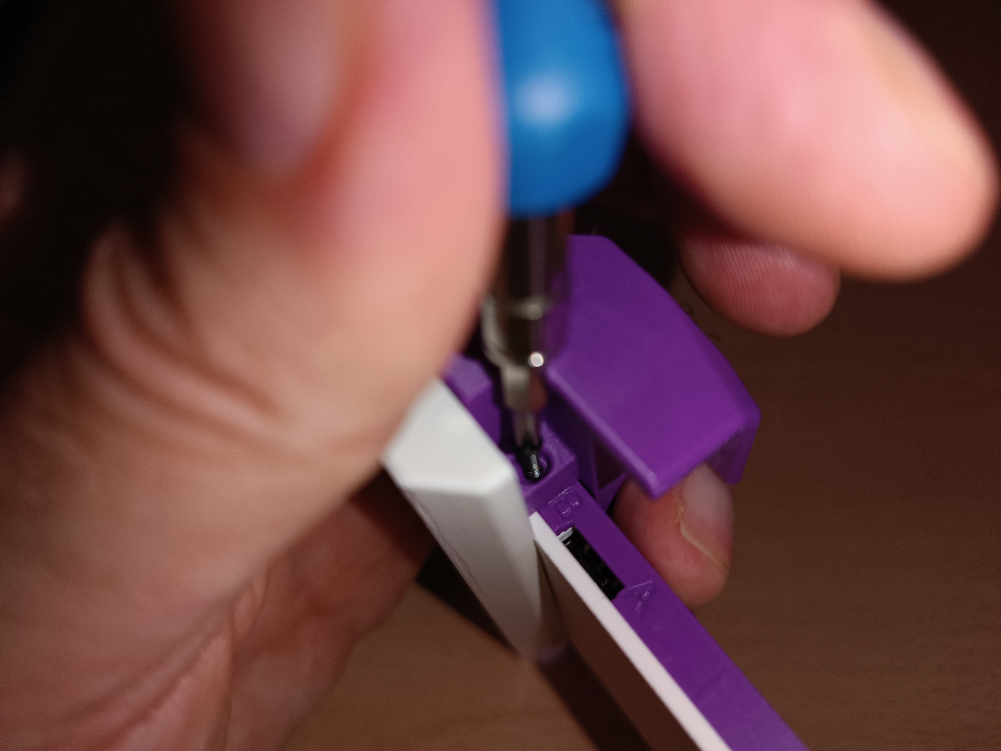
case_mounting/Step07_Screw_case_sidesB.jpg
