RndMnkIII/Analogizer/case_mounting/Step07_Screw_case_sidesC.jpg

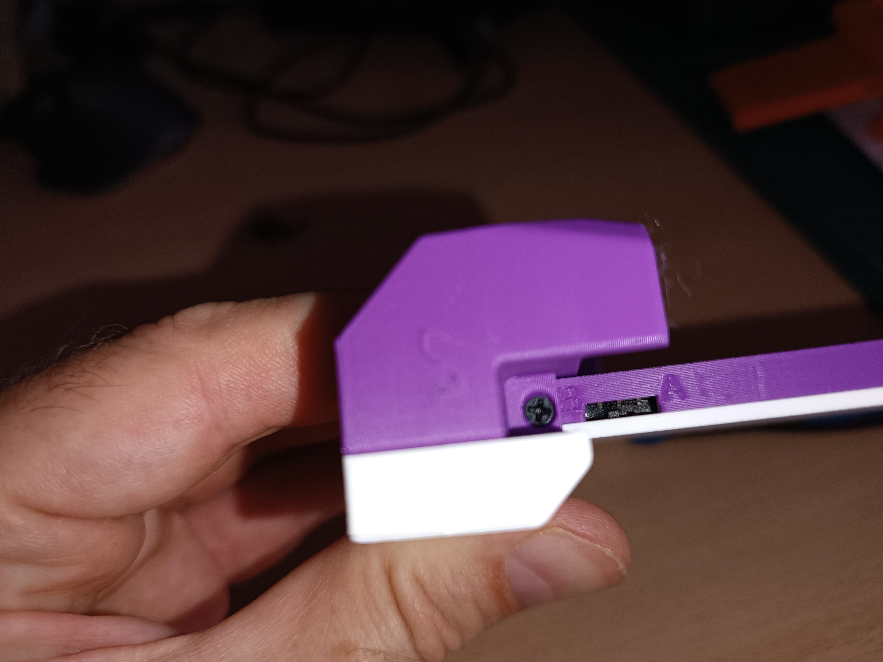
case_mounting/Step07_Screw_case_sidesC.jpg
