RndMnkIII/Analogizer/case_mounting/Step08_Completed_case_mount.jpg

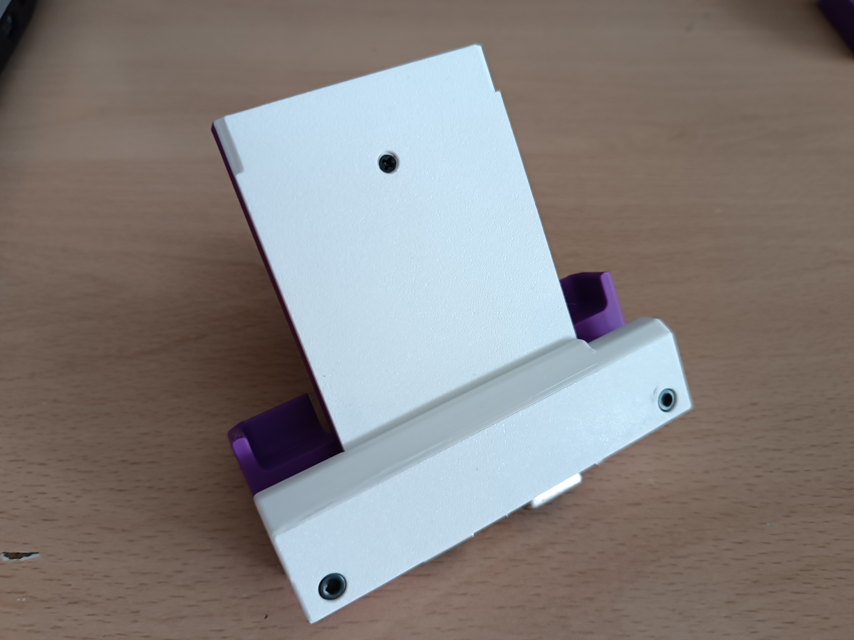
case_mounting/Step08_Completed_case_mount.jpg
