RndMnkIII/Analogizer/case_mounting/Step08_Screw_case_Base_A.jpg

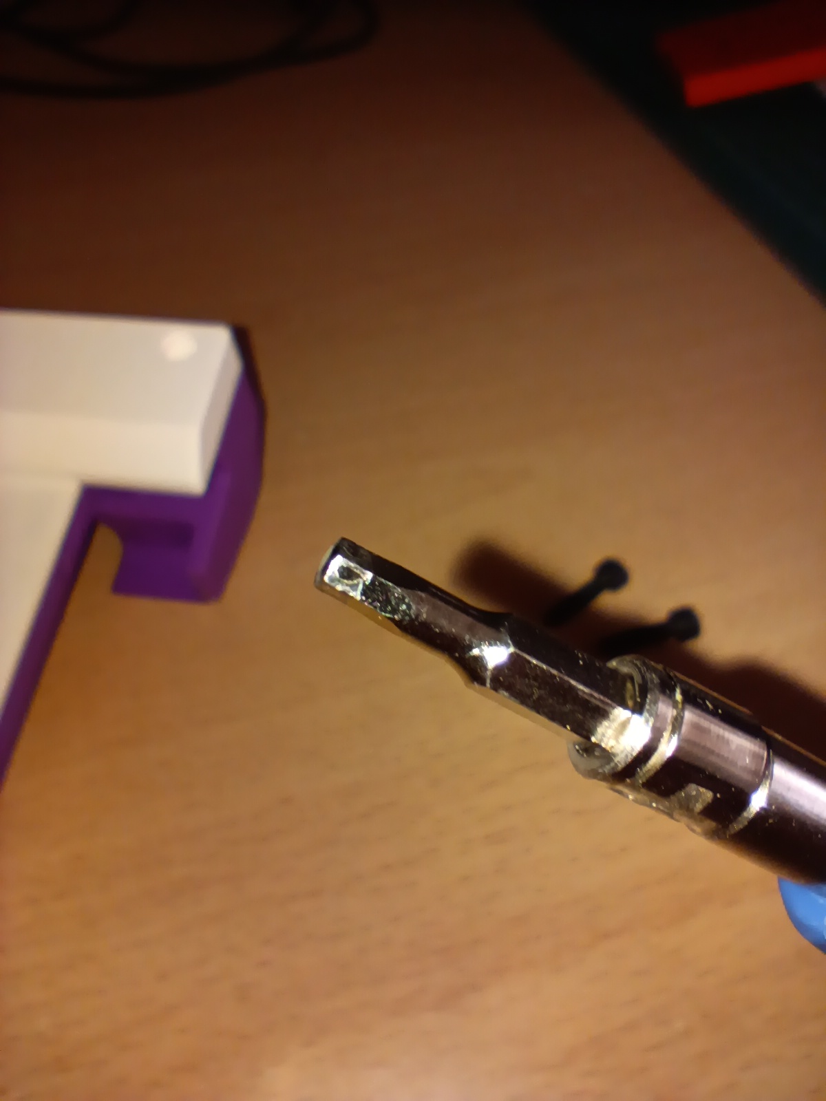
case_mounting/Step08_Screw_case_Base_A.jpg
