RndMnkIII/Analogizer/case_mounting/Step08_Screw_case_Base_B.jpg

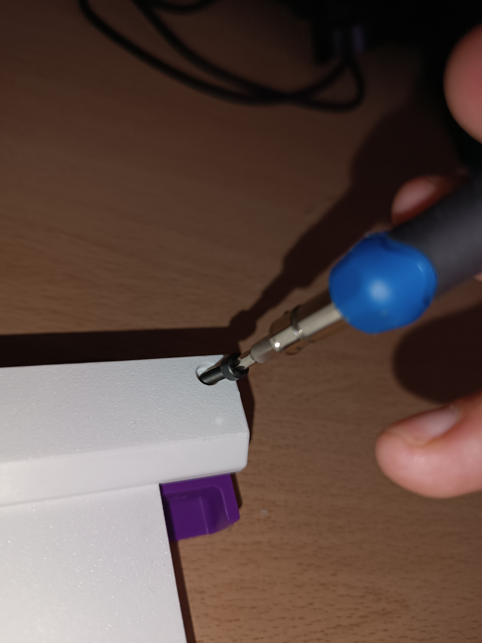
case_mounting/Step08_Screw_case_Base_B.jpg
