RndMnkIII/Analogizer/JT_cores_configurator/how_to_use1.PNG

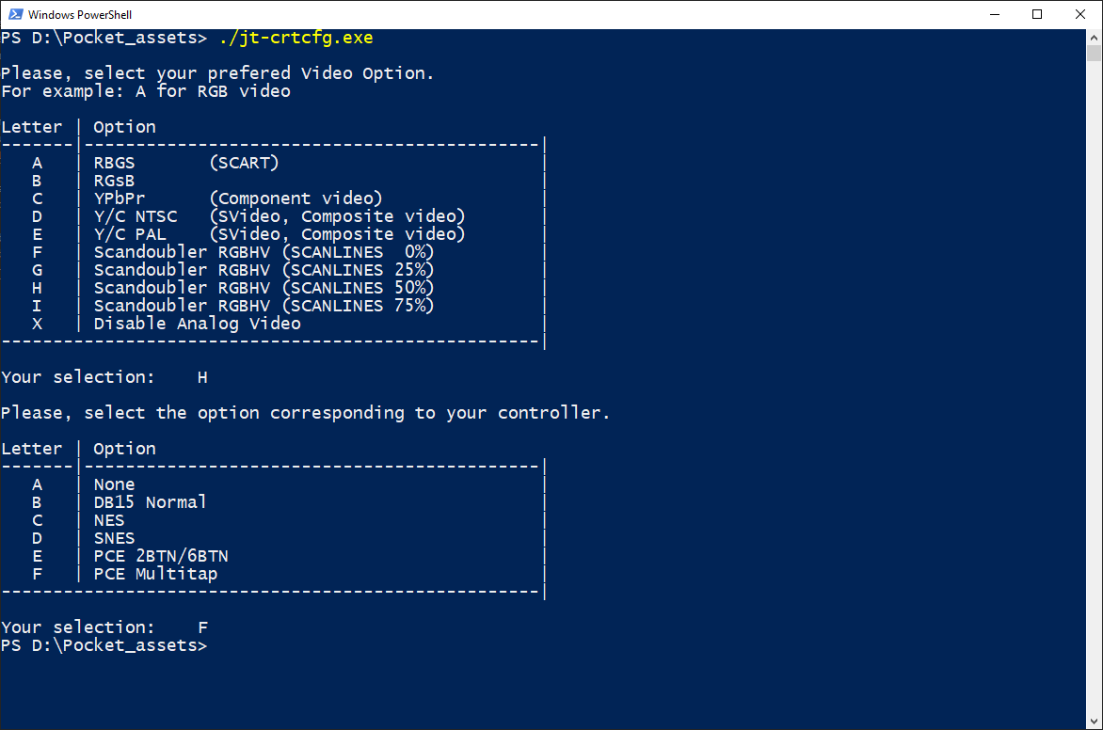
JT_cores_configurator/how_to_use1.PNG
