RndMnkIII/Analogizer/JT_cores_configurator/how_to_use2.PNG

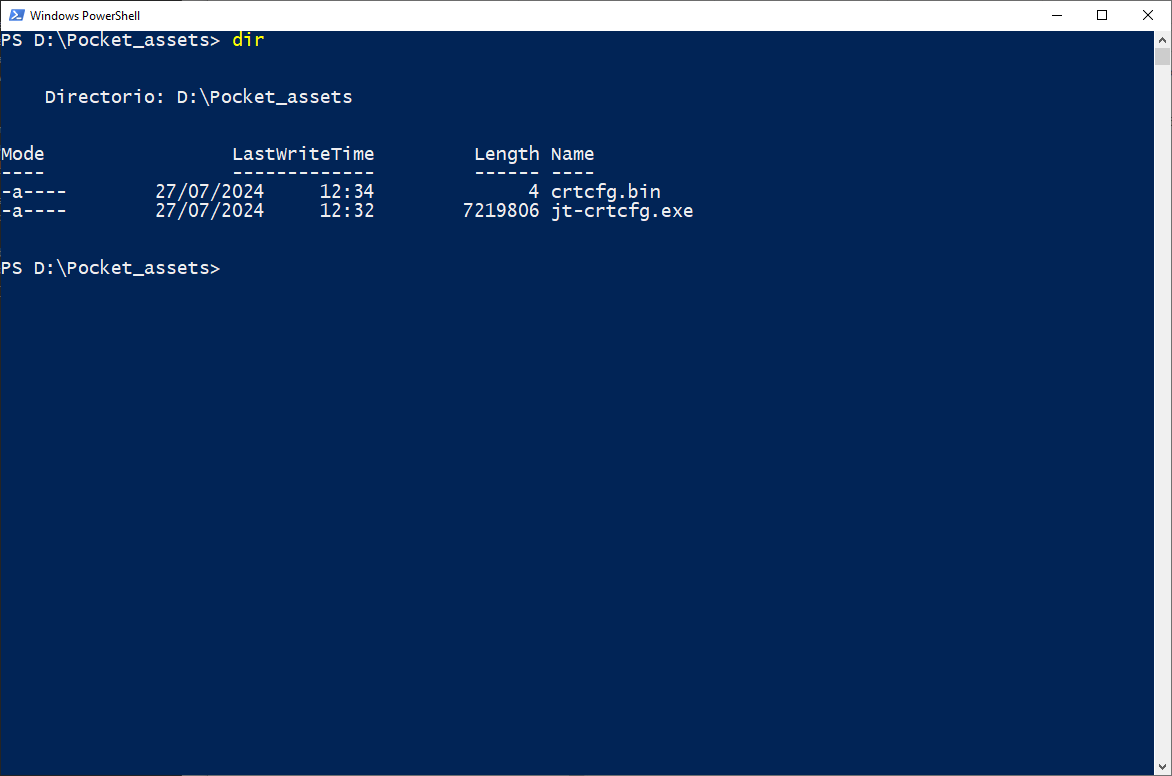
JT_cores_configurator/how_to_use2.PNG
