RndMnkIII/Analogizer/JT_cores_configurator/how_to_use3.PNG

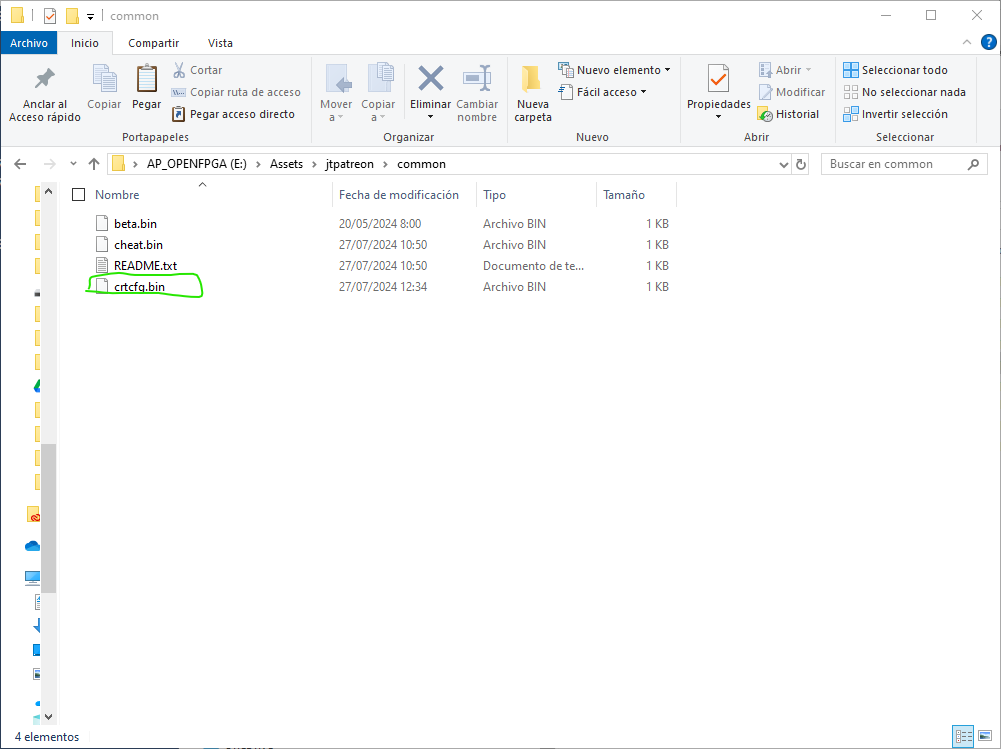
JT_cores_configurator/how_to_use3.PNG
