RndMnkIII/Analogizer/analogizer/openFPGA_Pocket_Analogizer.v

//This module encapsulates all Analogizer adapter signals
// Original work by @RndMnkIII. 
// Date: 05/2024 
// Releases: 
// 1.0 Initial RGBS output mode
// 1.1 Added SOG modes: RGsB, YPbPt
// 1.2 Added Mike Simon Y/C module, Scandoubler SVGA Mist module.     

// *** Analogizer R.2 adapter ***
// * WHEN SOG SWITCH IS IN ON POSITION, OUTPUTS CSYNC ON G CHANNEL
// # WHEN YPbPr VIDEO OUTPUT IS SELECTED, Y->G, Pr->R, Pb->B
//Pin mappings:                                               VGA CONNECTOR                                                                                          USB3 TYPE A FEMALE CONNECTOR (SNAC)
//                        ______________________________________________________________________________________________________________________________________________________________________________________________________                             
//                       /                              VS  HS          R#  G*# B#                                                                  1      2       3       4      5       6       7       8       9              \
//                       |                              |   |           |   |   |                                                                 VBUS   D-      D+      GND     RX-     RX+     GND_D   TX-     TX+             |
//FUNCTION:              |                              |   |           |   |   |                                                                 +5V    OUT1    OUT2    GND     IO3     IN4     IO5     IO6     IN7             |
//                       |  A                           |   |           |   |   |                                                                          ^       ^              ^       |       ^       ^       |              |
//                       |  N             SOG           |   |           |   |   |                                                                          |       |              V       V       V       V       V              |
//                       |  A           -------         |   |           |   |   |                                                                                                                                                |                              
//                       |  O    OFF   |   S   |--GND   |   |         +------------+                                                                                                                                             |
//                       |  L          |   W   |        |   |   SYNC  |            |                                                                                                                                             |            
//  PIN DIR:             |  G          |   I   +--------------------->|            |---------------------------------------------------------------------------------------------------------+                                   |
//  ^ OUTPUT             |  I          |   T   |        |   |         |  RGB DAC   |                                                                                                         |                                   |
//  V INPUT              |  Z          |   C   |        |   |         |            |===================================================================++                                    |                                   |
//                       |  E    ON ===|   H   |--------+   |         +------------+                                                                   ||                                    |                                   |
//                       |  R           -------         |   |            ||  |   | /BLANK                                                              ||                                    |                                   |         
//                       |                              |   +--------+   ||  |   +------------------------------------------------------------------+  ||                                    |                                   |                                  |
//                       |  R                           +------+     |   ||  +===============================++                                     |  ||                                    |                                   |
//                       |  2                                  |     |   ||                                  ||                                     |  ||                                    |                                   |
//                       |     CONF.B        IO5V       ---    |     |   \\================================  \\================================     |  \\================================   VID               IO3^  IO6^         |  
//                       |     CONF.A   IN4  ---  IN7   IO3V   VS    HS    R0    R1    R2    R3    R4    R5    G0    G1    G2    G3    G4    G5   /BLK   B0    B1    B2    B3    B4    B5   CLK  OUT1   OUT2  IO5^  IO6V         |  
//                       |      __3.3V__ |___ | __ |_____|_____|_____|_____|_____|_____|_____|_____|_____|_____|_____|_____|_____|_____|_____|_____|_____|_____|_____|_____|_____|_____|_____|_____|_____|_____|_____^__GND__    |                                
//POCKET                 |     /         V    V    V     V     ^     ^     ^     ^     ^     ^     ^     ^     ^     ^     ^     ^     ^     ^     ^     ^     ^     ^     ^     ^     ^     ^     ^     ^     ^     V       \   | 
//CARTRIDGE PIN #:       \____|     1    2    3    4     5     6     7     8     9    10    11    12    13    14    15    16    17    18    19    20    21    22    23    24    25    26    27    28    29    30    31   32  |___/
//                             \_________|____|____|_____|_____|_____|_____|_____|_____|_____|_____|_____|_____|_____|_____|_____|_____|_____|_____|_____|_____|_____|_____|_____|_____|_____|_____|_____|_____|_____|_______/
//Pocket Pin Name:                       |    |    |     |     |     |     |     |     |     |     |     |     |     |     |     |     |     |     |     |     |     |     |     |     |     |     |     |     |     | 
//cart_tran_bank0[7] --------------------+    |    |     |     |     |     |     |     |     |     |     |     |     |     |     |     |     |     |     |     |     |     |     |     |     |     |     |     |     | 
//cart_tran_bank0[6] -------------------------+    |     |     |     |     |     |     |     |     |     |     |     |     |     |     |     |     |     |     |     |     |     |     |     |     |     |     |     |
//cart_tran_bank0[5] ------------------------------+     |     |     |     |     |     |     |     |     |     |     |     |     |     |     |     |     |     |     |     |     |     |     |     |     |     |     |
//cart_tran_bank0[4] ------------------------------------+     |     |     |     |     |     |     |     |     |     |     |     |     |     |     |     |     |     |     |     |     |     |     |     |     |     |
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
//cart_tran_bank1[1] ------------------------------------------------------------------------------------------------------------------------------------------------+     |     |     |     |     |     |     |     |
//cart_tran_bank1[2] ------------------------------------------------------------------------------------------------------------------------------------------------------+     |     |     |     |     |     |     |
//cart_tran_bank1[3] ------------------------------------------------------------------------------------------------------------------------------------------------------------+     |     |     |     |     |     |
//cart_tran_bank1[4] ------------------------------------------------------------------------------------------------------------------------------------------------------------------+     |     |     |     |     |
//cart_tran_bank1[5] ------------------------------------------------------------------------------------------------------------------------------------------------------------------------+     |     |     |     |
//cart_tran_bank1[6] ------------------------------------------------------------------------------------------------------------------------------------------------------------------------------+     |     |     |
//cart_tran_bank1[7] ------------------------------------------------------------------------------------------------------------------------------------------------------------------------------------+     |     |
//cart_tran_pin30    ------------------------------------------------------------------------------------------------------------------------------------------------------------------------------------------+     | 
//cart_tran_pin31    ------------------------------------------------------------------------------------------------------------------------------------------------------------------------------------------------+
`default_nettype none
`timescale 1ns / 1ps

module openFPGA_Pocket_Analogizer #(parameter MASTER_CLK_FREQ=50_000_000, parameter LINE_LENGTH) (
	input wire i_clk,
    input wire i_rst,
	input wire i_ena,
	//Video interface
	input wire video_clk,
	input wire [3:0] analog_video_type,
	input wire [7:0] R,
	input wire [7:0] G,
	input wire [7:0] B,
	input wire Hblank,
	input wire Vblank,
	input wire BLANKn,
	input wire Hsync,
	input wire Vsync,
	input wire Csync,
	//Video Y/C Encoder interface
	input wire [39:0] CHROMA_PHASE_INC,
	input wire PALFLAG,
	//Video SVGA Scandoubler interface
	input wire ce_pix,
	input wire scandoubler, //logic for disable/enable the scandoubler
	input wire [2:0] fx, //0 disable, 1 scanlines 25%, 2 scanlines 50%, 3 scanlines 75%, 4 hq2x
	//SNAC interface
    input wire conf_AB,              //0 conf. A(default), 1 conf. B (see graph above)
    input wire [4:0] game_cont_type, //0-15 Conf. A, 16-31 Conf. B
    output wire [15:0] p1_btn_state,
	output wire [31:0] p1_joy_state,
    output wire [15:0] p2_btn_state,
	output wire [31:0] p2_joy_state,
    output wire [15:0] p3_btn_state,
    output wire [15:0] p4_btn_state,
	//PSX rumble interface joy1, joy2
    input [1:0] i_VIB_SW1,  //  Vibration SW  VIB_SW[0] Small Moter OFF 0:ON  1:
                                //VIB_SW[1] Bic Moter   OFF 0:ON  1(Dualshook Only)
	input [7:0] i_VIB_DAT1,  //  Vibration(Bic Moter)Data   8'H00-8'HFF (Dualshook Only)
    input [1:0] i_VIB_SW2,
	input [7:0] i_VIB_DAT2, 
	// 
	output wire busy, 
	//Pocket Analogizer IO interface to the cartridge port
	inout   wire    [7:0]   cart_tran_bank2,
	output  wire            cart_tran_bank2_dir,
	inout   wire    [7:0]   cart_tran_bank3,
	output  wire            cart_tran_bank3_dir,
	inout   wire    [7:0]   cart_tran_bank1,
	output  wire            cart_tran_bank1_dir,
	inout   wire    [7:4]   cart_tran_bank0,
	output  wire            cart_tran_bank0_dir,
	inout   wire            cart_tran_pin30,
	output  wire            cart_tran_pin30_dir,
	output  wire            cart_pin30_pwroff_reset,
	inout   wire            cart_tran_pin31,
	output  wire            cart_tran_pin31_dir,
    //debug
	output wire [3:0] DBG_TX,
    output wire o_stb
);
	wire [7:4] CART_BK0_OUT ;
    wire [7:4] CART_BK0_IN ;
    wire CART_BK0_DIR ; 
    wire [7:6] CART_BK1_OUT_P76 ;
    wire CART_PIN30_OUT ;
    wire CART_PIN30_IN ;
    wire CART_PIN30_DIR ; 
    wire CART_PIN31_OUT ;
    wire CART_PIN31_IN ;
    wire CART_PIN31_DIR ;

	openFPGA_Pocket_Analogizer_SNAC #(.MASTER_CLK_FREQ(MASTER_CLK_FREQ)) snac
	(
		.i_clk(i_clk),
		.i_rst(i_rst),
		.conf_AB(conf_AB),              //0 conf. A(default), 1 conf. B (see graph above)
		.game_cont_type(game_cont_type), //0-15 Conf. A, 16-31 Conf. B
		//.game_cont_sample_rate(game_cont_sample_rate), //0 compatibility mode (slowest), 1 normal mode, 2 fast mode, 3 superfast mode
		.p1_btn_state(p1_btn_state),
		.p1_joy_state(p1_joy_state),
		.p2_btn_state(p2_btn_state),
		.p2_joy_state(p2_joy_state),
		.p3_btn_state(p3_btn_state),
		.p4_btn_state(p4_btn_state),
		.i_VIB_SW1(i_VIB_SW1), .i_VIB_DAT1(i_VIB_DAT1), .i_VIB_SW2(i_VIB_SW2), .i_VIB_DAT2(i_VIB_DAT2), 
		.busy(busy),    
		//SNAC Pocket cartridge port interface (see graph above)   
		.CART_BK0_OUT(CART_BK0_OUT),
		.CART_BK0_IN(CART_BK0_IN),
		.CART_BK0_DIR(CART_BK0_DIR), 
		.CART_BK1_OUT_P76(CART_BK1_OUT_P76),
		.CART_PIN30_OUT(CART_PIN30_OUT),
		.CART_PIN30_IN(CART_PIN30_IN),
		.CART_PIN30_DIR(CART_PIN30_DIR), 
		.CART_PIN31_OUT(CART_PIN31_OUT),
		.CART_PIN31_IN(CART_PIN31_IN),
		.CART_PIN31_DIR(CART_PIN31_DIR),
		//debug
		.DBG_TX(DBG_TX),
    	.o_stb(o_stb)
	); 

	//Choose type of analog video type of signal
	reg [5:0] Rout, Gout, Bout /* synthesis preserve */;
	reg HsyncOut, VsyncOut, BLANKnOut /* synthesis preserve */;
	wire [7:0] Yout, PrOut, PbOut /* synthesis keep */;
	wire [7:0] R_Sd, G_Sd, B_Sd /* synthesis keep */;
	wire Hsync_Sd, Vsync_Sd /* synthesis keep */;
	wire Hblank_Sd, Vblank_Sd /* synthesis keep */;
	//wire BLANKn_SD = ~(Hblank_Sd || Vblank_Sd) /* synthesis keep */;

	always @(*) begin
		case(analog_video_type)
			4'h0, 4'h8: begin //RGBS
				Rout = R[7:2]&{6{BLANKn}};
				Gout = G[7:2]&{6{BLANKn}};
				Bout = B[7:2]&{6{BLANKn}};
				HsyncOut = Csync;
				VsyncOut = 1'b1;
				BLANKnOut = BLANKn;
			end
			4'h3, 4'h4, 4'hB, 4'hC: begin// Y/C Modes works for Analogizer R1, R2 Adapters
				Rout = yc_o[23:18];
				Gout = yc_o[15:10];
				Bout = yc_o[7:2];
				HsyncOut = yc_cs;
				VsyncOut = 1'b1;
				BLANKnOut = 1'b1;
			end
			4'h1, 4'h9: begin //RGsB
				Rout = R[7:2]&{6{BLANKn}};
				Gout = G[7:2]&{6{BLANKn}};
				Bout = B[7:2]&{6{BLANKn}};
				HsyncOut = 1'b1;
				VsyncOut = Csync; //to DAC SYNC pin, SWITCH SOG ON
				BLANKnOut = BLANKn;
			end
			4'h2, 4'hA: begin //YPbPr
				Rout = PrOut[7:2];
				Gout = Yout[7:2];
				Bout = PbOut[7:2];
				HsyncOut = 1'b1;
				VsyncOut = YPbPr_sync; //to DAC SYNC pin, SWITCH SOG ON
				BLANKnOut = 1'b1; //ADV7123 needs this
			end
			// 4'h5, 4'h6, 4'h7, 4'hD, 4'hE, 4'hF: begin //Scandoubler modes
			// 	Rout = vga_data_sl[23:18]; //R_Sd[7:2];
			// 	Gout = vga_data_sl[15:10]; //G_Sd[7:2];
			// 	Bout = vga_data_sl[7:2]; //B_Sd[7:2];
			// 	HsyncOut = vga_hs_sl; //Hsync_Sd;
			// 	VsyncOut = vga_vs_sl; //Vsync_Sd;
			// 	BLANKnOut = 1'b1;
			// end
			4'h5, 4'h6, 4'h7, 4'hD, 4'hE, 4'hF: begin //Scandoubler modes Old Scandoubler module
				Rout = R_Sd;
				Gout = G_Sd;
				Bout = B_Sd;
				HsyncOut = Hsync_Sd;
				VsyncOut = Vsync_Sd;
				BLANKnOut = 1'b1;
			end
			default: begin
				Rout = 6'h0;
				Gout = 6'h0;
				Bout = 6'h0;
				HsyncOut = Hsync;
				VsyncOut = 1'b1;
				BLANKnOut = BLANKn;
			end
		endcase
	end


	//First Stage: video fix
	// wire hs_fix,vs_fix;
	// sync_fix sync_v(video_clk, HSync, hs_fix);
	// sync_fix sync_h(video_clk, VSync, vs_fix);

	// reg [DW-1:0] RGB_fix;

	// reg CE_fix,HS_fix,VS_fix,HBL_fix,VBL_fix;
	// always @(posedge video_clk) begin
	// 	reg old_ce;
	// 	old_ce <= ce_pix;
	// 	CE_fix <= 0;
	// 	if(~old_ce & ce_pix) begin
	// 		CE_fix <= 1;
	// 		HS_fix <= hs_fix;
	// 		if(~HS_fix & hs_fix) VS_fix <= vs_fix;

	// 		RGB_fix <= {R,G,B};
	// 		HBL_fix <= HBlank;
	// 		if(HBL_fix & ~HBlank) VBL_fix <= VBlank;
	// 	end
	// end

	// //Csync generation
	// wire CSYNC_fix;
	// csync csync_fix(video_clk, HS_fix, VS_fix, CSYNC_fix);

	wire YPbPr_sync, YPbPr_blank;
	vga_out ybpr_video
	(
		.clk(video_clk),
		.ypbpr_en(1'b1),
		.csync(Csync),
		.de(BLANKn),
		.din({R&{8{BLANKn}},G&{8{BLANKn}},B&{8{BLANKn}}}), //NES specific override, because not zero color data while blanking period.
		.dout({PrOut,Yout,PbOut}),
		.csync_o(YPbPr_sync),
		.de_o(YPbPr_blank)
	);

	wire [23:0] yc_o /* synthesis keep */;
	//wire yc_hs, yc_vs, 
	wire yc_cs /* synthesis keep */;
	yc_out yc_out
	(
		.clk(i_clk),
		.PHASE_INC(CHROMA_PHASE_INC),
		.PAL_EN(PALFLAG),
		.hsync(Hsync),
		.vsync(Vsync),
		.csync(Csync),
    	.din({R&{8{BLANKn}},G&{8{BLANKn}},B&{8{BLANKn}}}),
		.dout(yc_o),
		.hsync_o(),
		.vsync_o(),
		.csync_o(yc_cs)
	);

	wire ce_pix_Sd /* synthesis keep */;
// 	scandoubler_2 #(.LENGTH(LINE_LENGTH), .HALF_DEPTH(0)) sd
// 	(
// 		.clk_vid(i_clk),
// 		.hq2x(fx[2]),

// 		.ce_pix(ce_pix),
// 		.hs_in(Hsync),
// 		.vs_in(Vsync),
// 		.hb_in(Hblank),
// 		.vb_in(Vblank),
// 		.r_in({R[7:0]&{8{BLANKn}}}),
// 		.g_in({G[7:0]&{8{BLANKn}}}),
// 		.b_in({B[7:0]&{8{BLANKn}}}),

// 		.ce_pix_out(ce_pix_Sd),
// 		.hs_out(Hsync_Sd),
// 		.vs_out(Vsync_Sd),
// 		.hb_out(Hblank_Sd),
// 		.vb_out(Vblank_Sd),
// 		.r_out(R_Sd),
// 		.g_out(G_Sd),
// 		.b_out(B_Sd)
// 	);

// 	reg Hsync_SL, Vsync_SL, Hblank_SL, Vblank_SL /* synthesis preserve */;
// 	reg [7:0] R_SL, G_SL, B_SL /* synthesis preserve */;
// 	reg CE_PIX_SL, DE_SL /* synthesis preserve */;

// 	always @(posedge video_clk) begin
// 		Hsync_SL <= (scandoubler) ? Hsync_Sd : Hsync;
// 		Vsync_SL <= (scandoubler) ? Vsync_Sd : Vsync;
// 		Hblank_SL <= (scandoubler) ? Hblank_Sd : Hblank;
// 		Vblank_SL <= (scandoubler) ? Vblank_Sd : Vblank;
// 		R_SL <= (scandoubler) ? R_Sd    : {R[7:0]&{8{BLANKn}}};
// 		G_SL <= (scandoubler) ? G_Sd    : {G[7:0]&{8{BLANKn}}};
// 		B_SL <= (scandoubler) ? B_Sd    : {B[7:0]&{8{BLANKn}}};
// 		CE_PIX_SL <= (scandoubler) ? ce_pix_Sd : ce_pix;
// 		DE_SL <= BLANKn;
// 	end


// wire [23:0] vga_data_sl /* synthesis keep */;
// wire        vga_vs_sl, vga_hs_sl /* synthesis keep */;
// scanlines_analogizer #(0) VGA_scanlines
// (
// 	.clk(video_clk),

// 	.scanlines(fx[1:0]),
// 	//.din(de_emu ? {R_SL, G_SL,B_SL} : 24'd0),
// 	.din({R_SL, G_SL,B_SL}),
// 	.hs_in(Hsync_SL),
// 	.vs_in(Vsync_SL),
// 	.de_in(DE_SL),
// 	.ce_in(CE_PIX_SL),

// 	.dout(vga_data_sl),
// 	.hs_out(vga_hs_sl),
// 	.vs_out(vga_vs_sl),
// 	.de_out(),
// 	.ce_out()
// );

	//Using old scandoubler code for PC Engine CD core
	scandoubler sc_video
	(
		// system interface
		.clk_sys(i_clk),
		.bypass(1'b0),

		// Pixelclock
		.ce_divider(3'd7), // 0 - clk_sys/4, 1 - clk_sys/2, 2 - clk_sys/3, 3 - clk_sys/4, etc.
		//.ce_divider(3'd0), // 0 - clk_sys/4, 1 - clk_sys/2, 2 - clk_sys/3, 3 - clk_sys/4, etc.
		.pixel_ena(), //output
		.scanlines(fx[1:0]), // scanlines (00-none 01-25% 10-50% 11-75%)

		// shifter video interface
		.hb_in(Hblank),
		.vb_in(Vblank),
		.hs_in(Hsync),
		//.hs_in(delayed_hsync[1]),
		.vs_in(Vsync),
		.r_in({R[7:2]&{6{BLANKn}}}),
		.g_in({G[7:2]&{6{BLANKn}}}),
		.b_in({B[7:2]&{6{BLANKn}}}),

		// output interface
		.hb_out(Hblank_Sd),
		.vb_out(Vblank_Sd),
		.hs_out(Hsync_Sd),
		.vs_out(Vsync_Sd),
		.r_out(R_Sd),
		.g_out(G_Sd),
		.b_out(B_Sd)
	);


	//infer tri-state buffers for cartridge data signals
	//BK0
	assign cart_tran_bank0         = i_rst | ~i_ena ? 4'hf : ((CART_BK0_DIR) ? CART_BK0_OUT : 4'hZ);     //on reset state set ouput value to 4'hf
	assign cart_tran_bank0_dir     = i_rst | ~i_ena ? 1'b1 : CART_BK0_DIR;                              //on reset state set pin dir to output
	assign CART_BK0_IN             = cart_tran_bank0;
	//BK3
	assign cart_tran_bank3         = i_rst | ~i_ena ? 8'hzz : {Rout[5:0],HsyncOut,VsyncOut};                          //on reset state set ouput value to 8'hZ
	assign cart_tran_bank3_dir     = i_rst | ~i_ena ? 1'b0  : 1'b1;                                     //on reset state set pin dir to input
	//BK2
	assign cart_tran_bank2         = i_rst | ~i_ena ? 8'hzz : {Bout[0],BLANKnOut,Gout[5:0]};                          //on reset state set ouput value to 8'hZ
	assign cart_tran_bank2_dir     = i_rst | ~i_ena ? 1'b0  : 1'b1;                                     //on reset state set pin dir to input
	//BK1
	assign cart_tran_bank1         = i_rst | ~i_ena ? 8'hzz : {CART_BK1_OUT_P76,video_clk,Bout[5:1]};      //on reset state set ouput value to 8'hZ
	assign cart_tran_bank1_dir     = i_rst | ~i_ena ? 1'b0  : 1'b1;                                     //on reset state set pin dir to input
	//PIN30
	assign cart_tran_pin30         = i_rst | ~i_ena ? 1'bz : ((CART_PIN30_DIR) ? CART_PIN30_OUT : 1'bZ); //on reset state set ouput value to 4'hf
	assign cart_tran_pin30_dir     = i_rst | ~i_ena ? 1'b0 : CART_PIN30_DIR;                              //on reset state set pin dir to output
	assign CART_PIN30_IN           = cart_tran_pin30;
	assign cart_pin30_pwroff_reset = i_rst | ~i_ena ? 1'b0 : 1'b1;                                      //1'b1 (GPIO USE)
	//PIN31
	assign cart_tran_pin31         = i_rst | ~i_ena ? 1'bz : ((CART_PIN31_DIR) ? CART_PIN31_OUT : 1'bZ); //on reset state set ouput value to 4'hf
	assign cart_tran_pin31_dir     = i_rst | ~i_ena ? 1'b0 : CART_PIN31_DIR;                            //on reset state set pin dir to input
	assign CART_PIN31_IN           = cart_tran_pin31;
endmodule
